backmeupplz/project-horae/media/2026-10-05/cad-charger.png

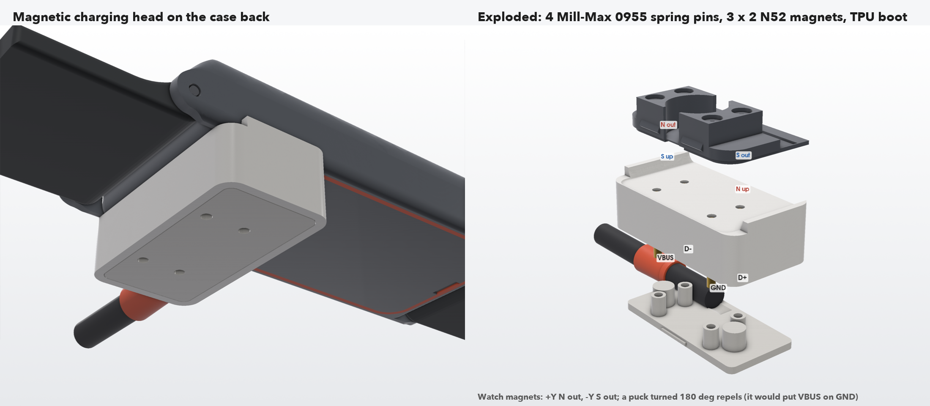
media/2026-10-05/cad-charger.png
