backmeupplz/project-horae/explorer/face.png

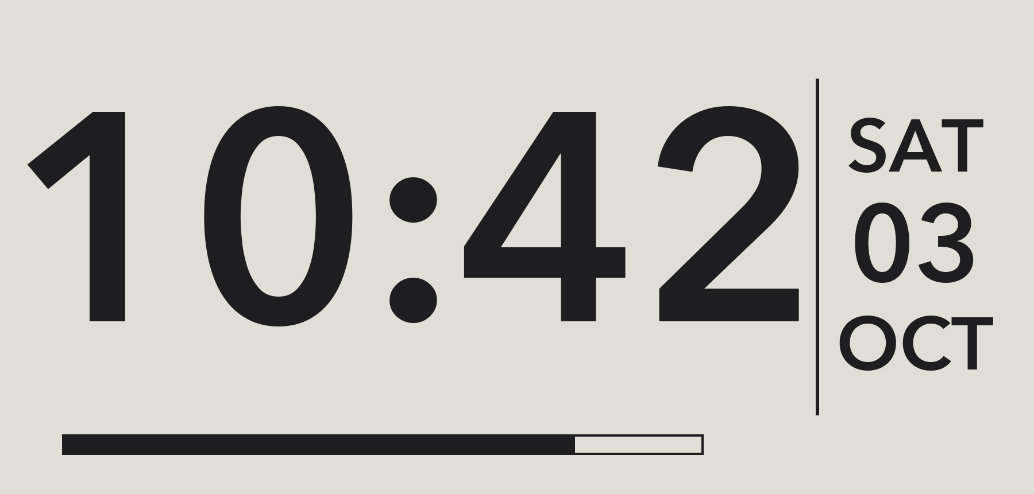
explorer/face.png
