backmeupplz/project-horae/hardware/out/panel-top.png

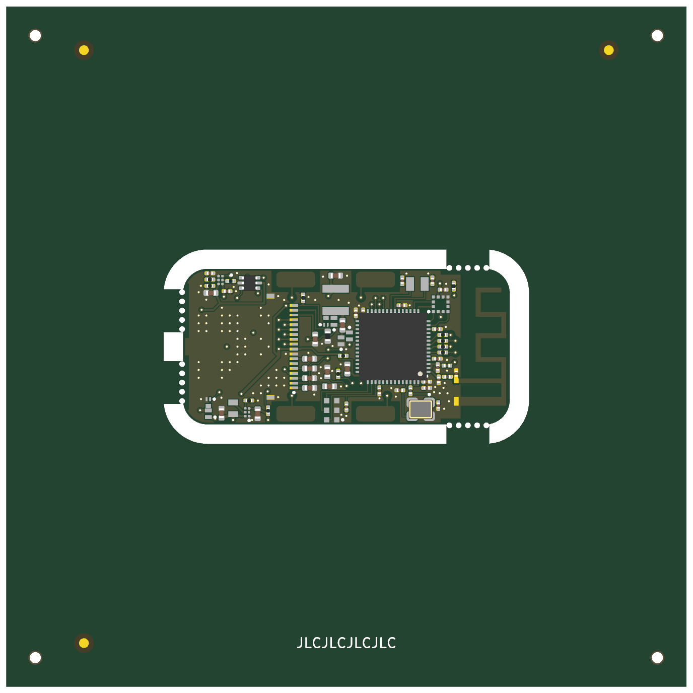
hardware/out/panel-top.png
