backmeupplz/project-horae/hardware/out/pcb-top.png

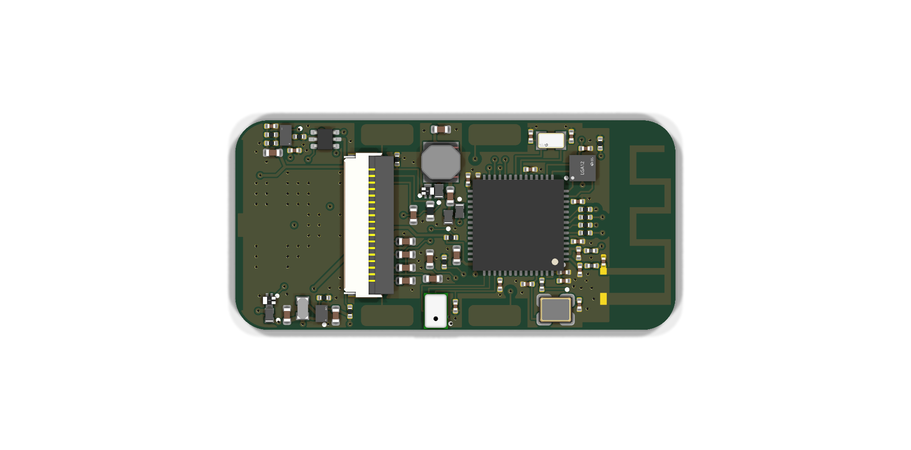
hardware/out/pcb-top.png
