backmeupplz/project-horae/hardware/rf/geom.png

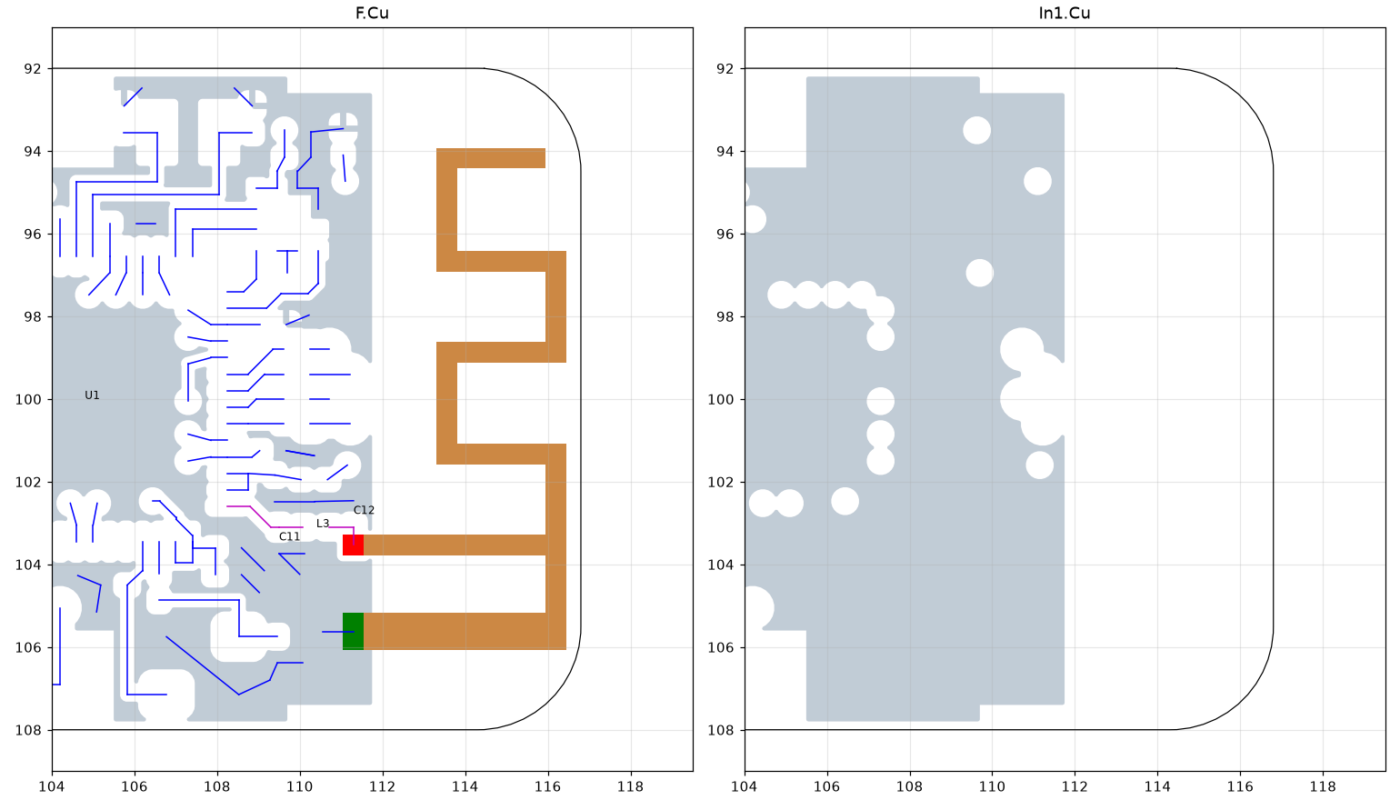
hardware/rf/geom.png
