backmeupplz/project-horae/hardware/rf/rf-s11.png

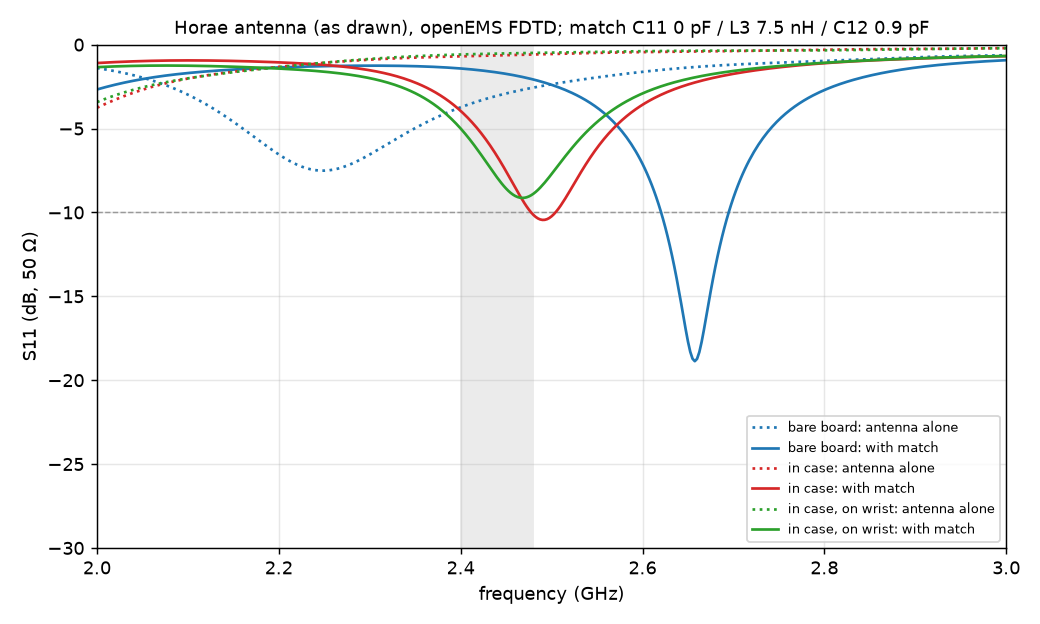
hardware/rf/rf-s11.png
