backmeupplz/project-horae/hardware/rf/rf-s11_v4_trim6.64.png

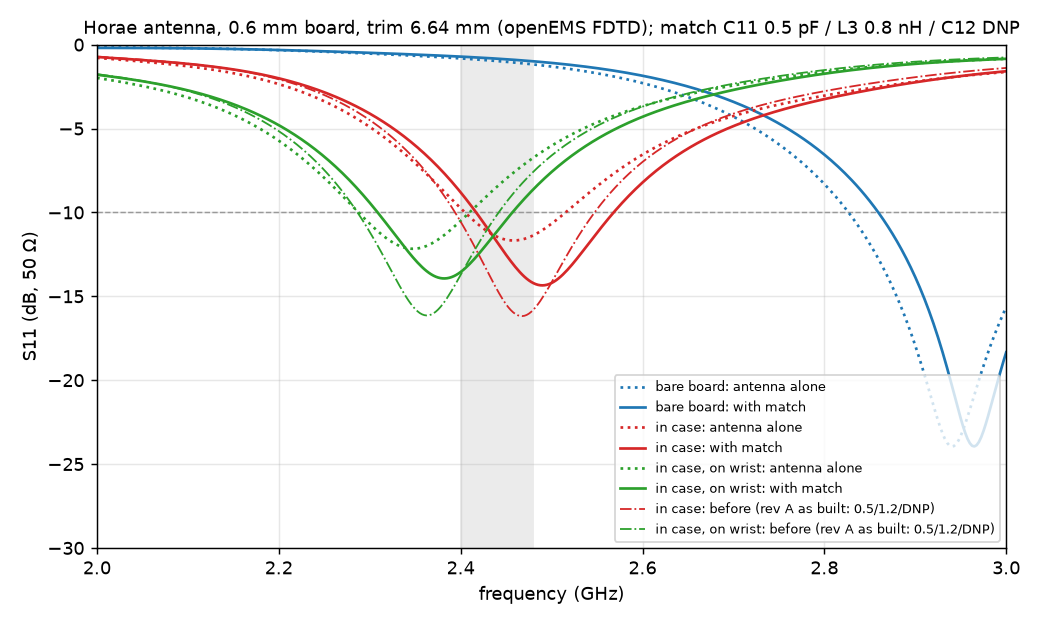
hardware/rf/rf-s11_v4_trim6.64.png
