backmeupplz/project-horae/hardware/rf/rf-smith_trim6.64.png

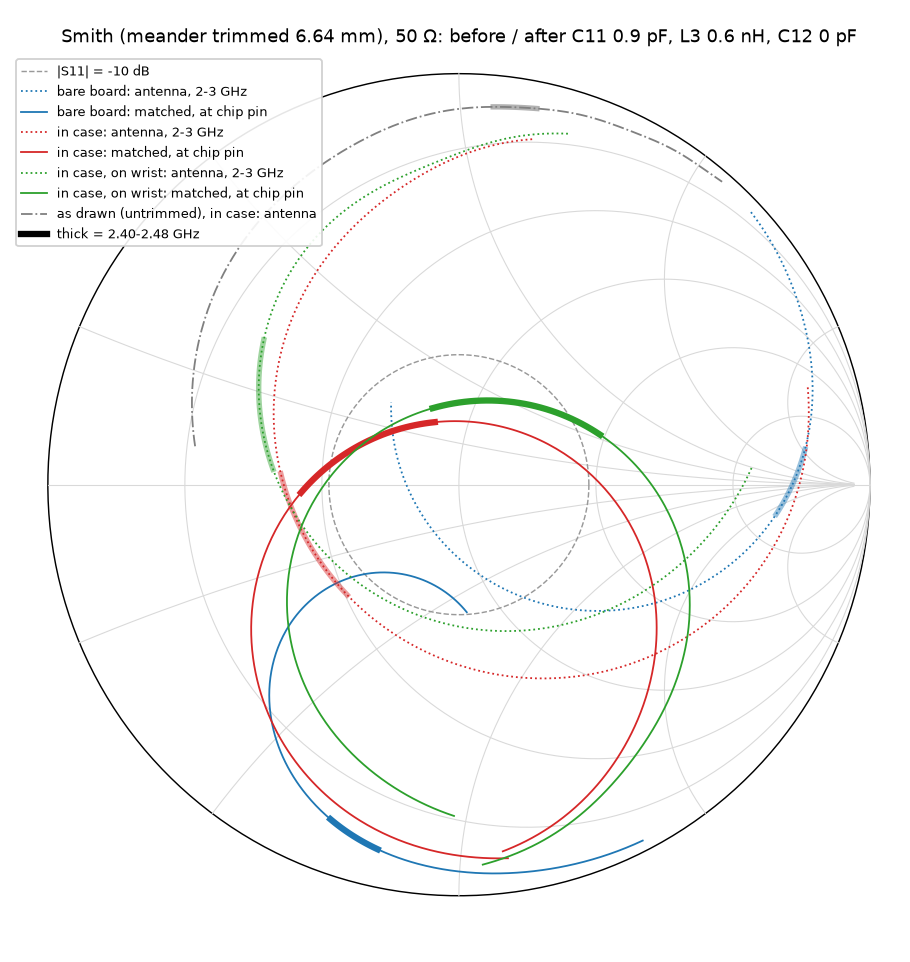
hardware/rf/rf-smith_trim6.64.png
