backmeupplz/project-horae/media/2026-10-03/box.jpg

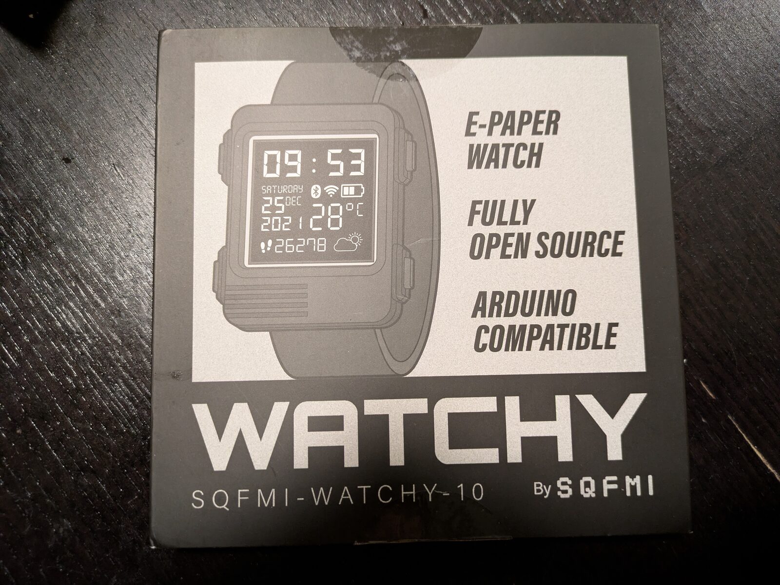
media/2026-10-03/box.jpg
