backmeupplz/project-horae/media/2026-10-03/inner-box.jpg

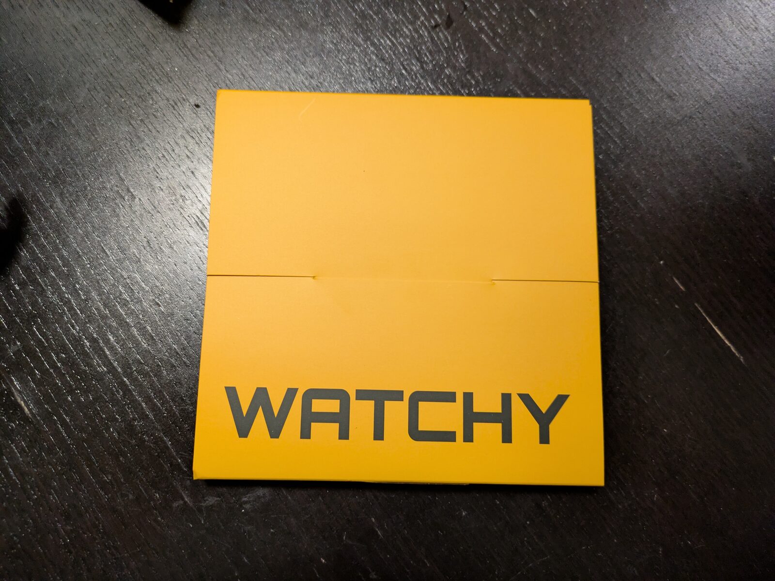
media/2026-10-03/inner-box.jpg
