backmeupplz/project-horae/media/2026-10-03/open.jpg

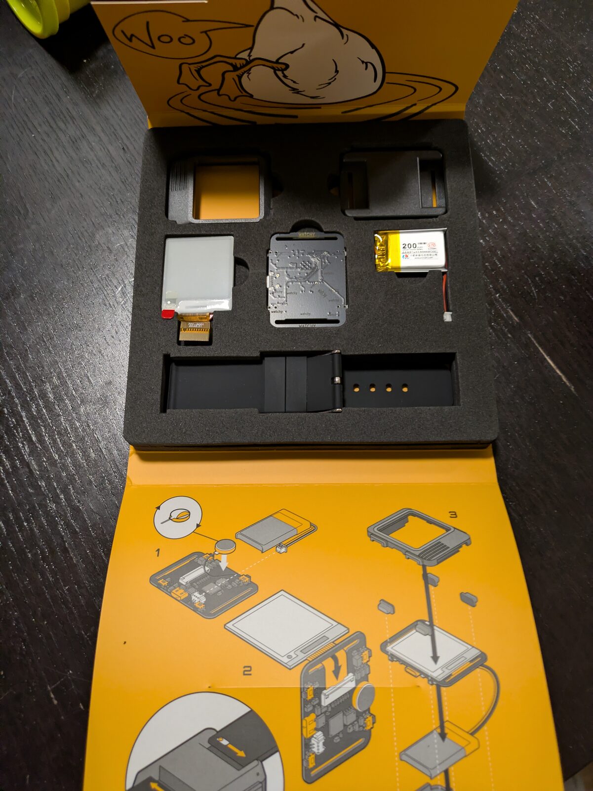
media/2026-10-03/open.jpg
