backmeupplz/project-horae/media/2026-10-04/cad-dock.png

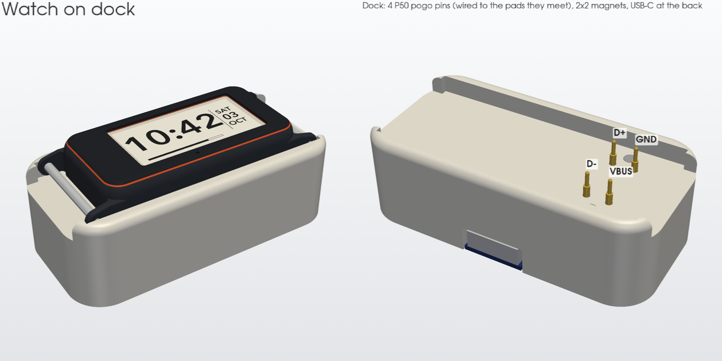
media/2026-10-04/cad-dock.png
