backmeupplz/project-horae/media/2026-10-04/cad-exploded.png

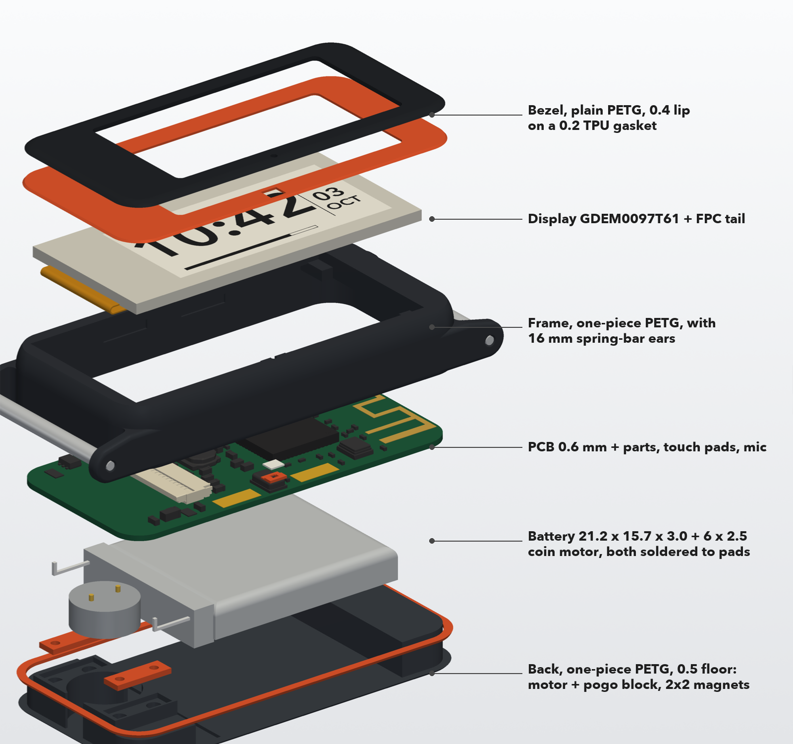
media/2026-10-04/cad-exploded.png
