backmeupplz/project-horae/media/2026-10-04/cad-mic.png

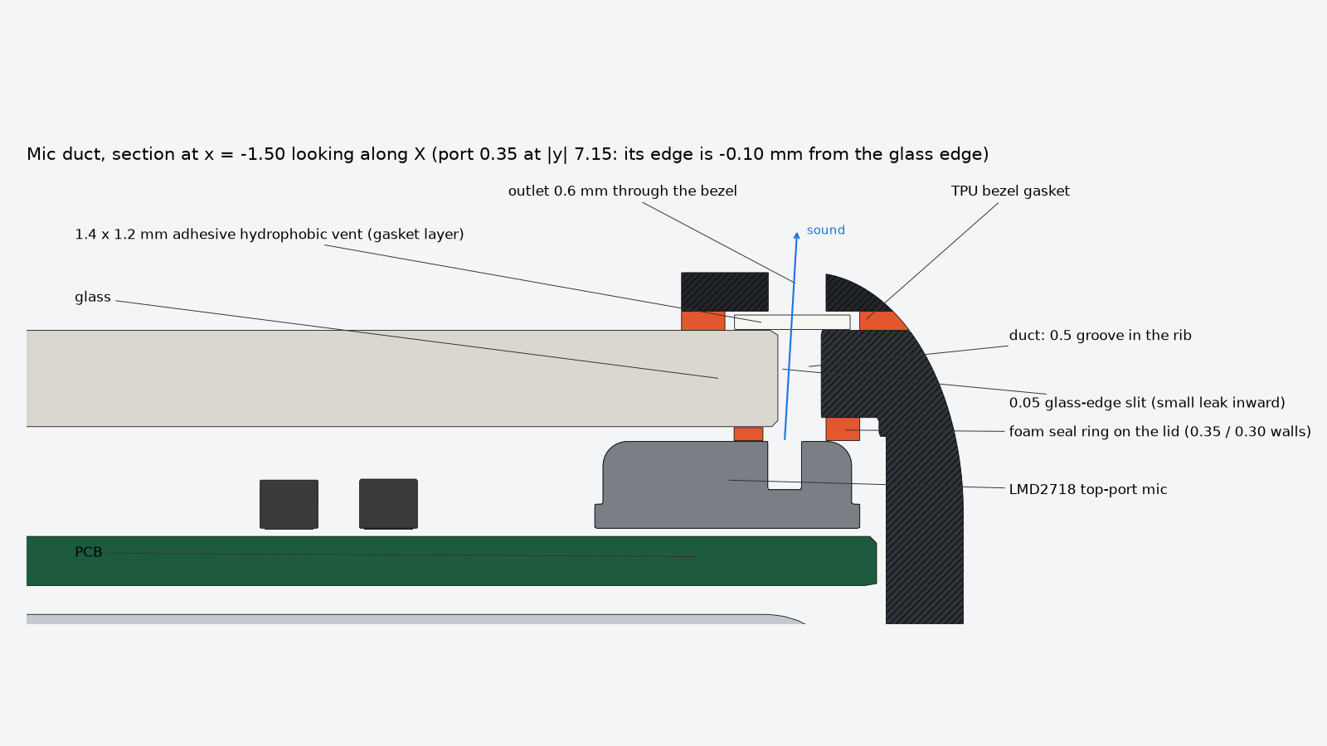
media/2026-10-04/cad-mic.png
