backmeupplz/project-horae/media/2026-10-04/cad-scale.png

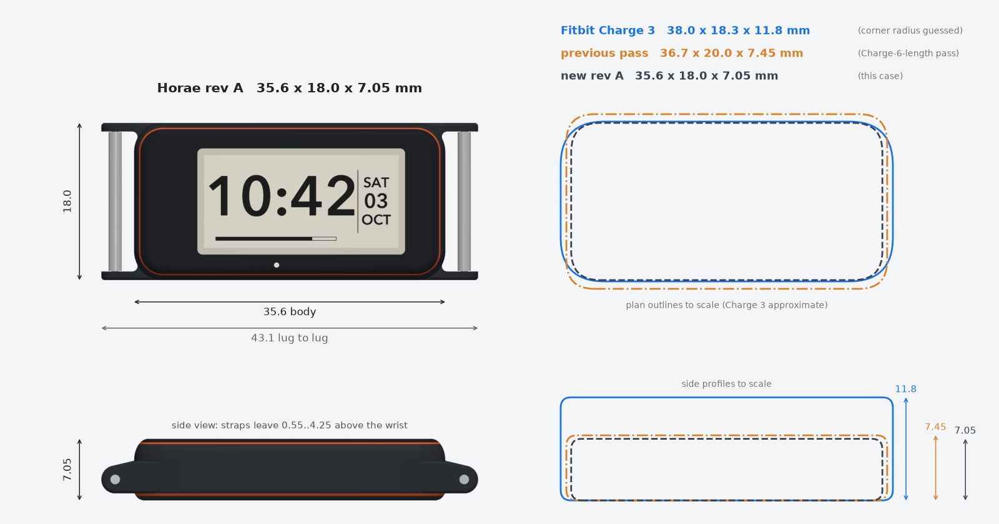
media/2026-10-04/cad-scale.png
