backmeupplz/project-horae/media/2026-10-04/cad-sealing.png

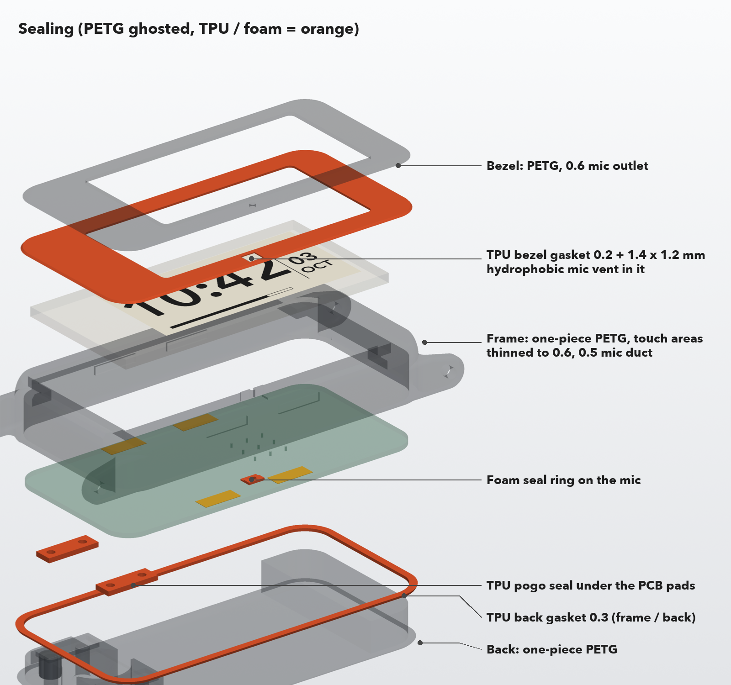
media/2026-10-04/cad-sealing.png
