backmeupplz/project-horae/media/2026-10-04/cad-section.png

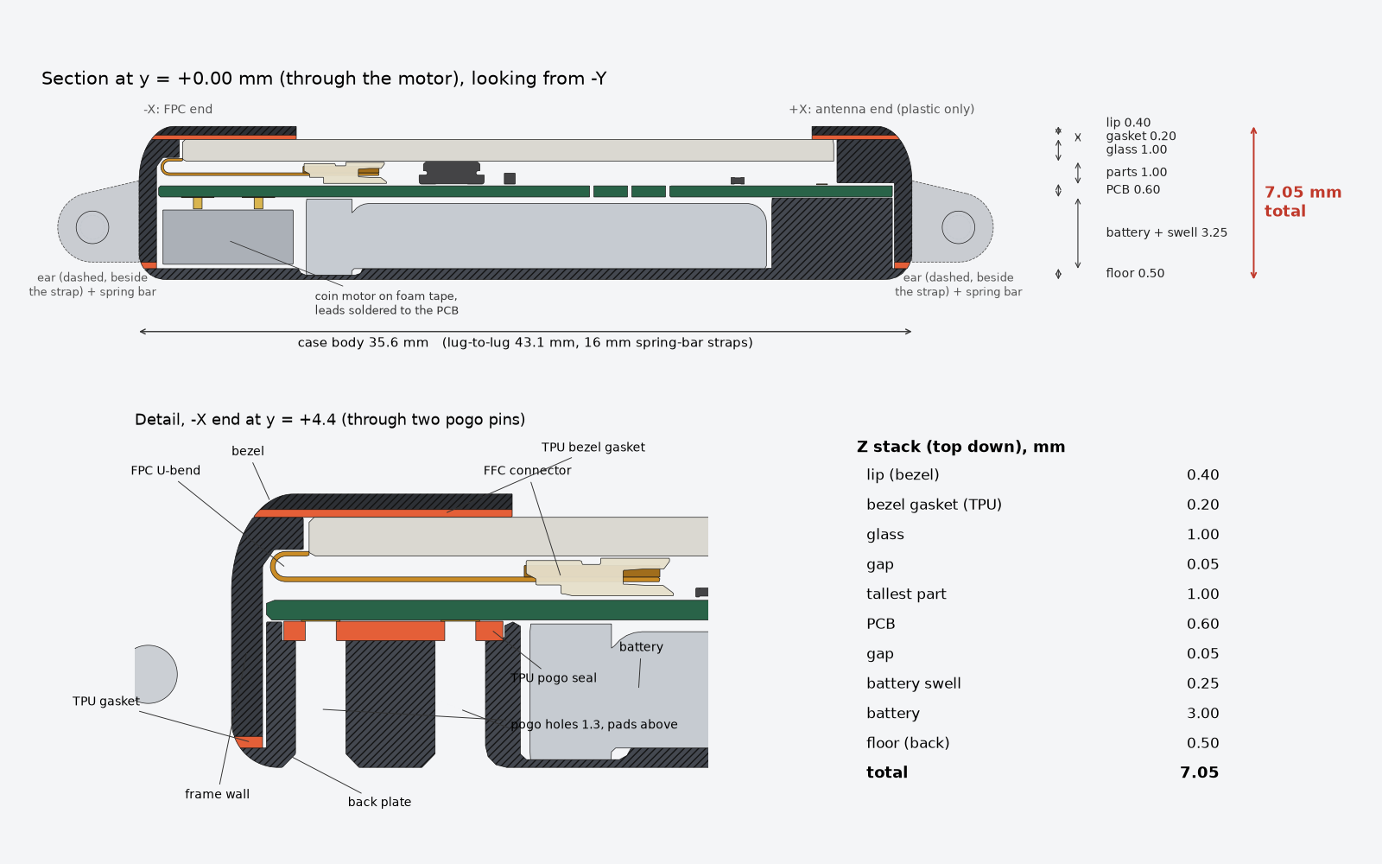
media/2026-10-04/cad-section.png
