backmeupplz/project-horae/media/2026-10-04/cad-shape-options.png

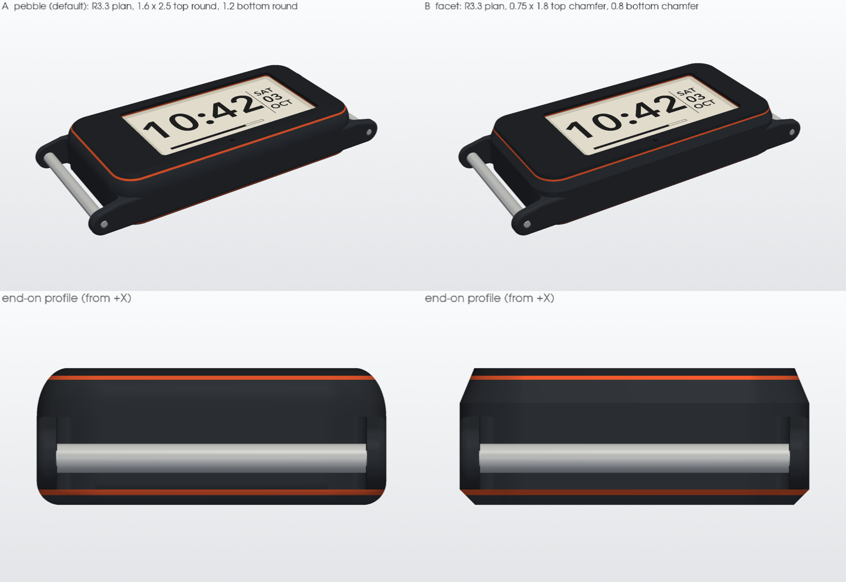
media/2026-10-04/cad-shape-options.png
