backmeupplz/project-horae/media/2026-10-04/pcb-3d.png

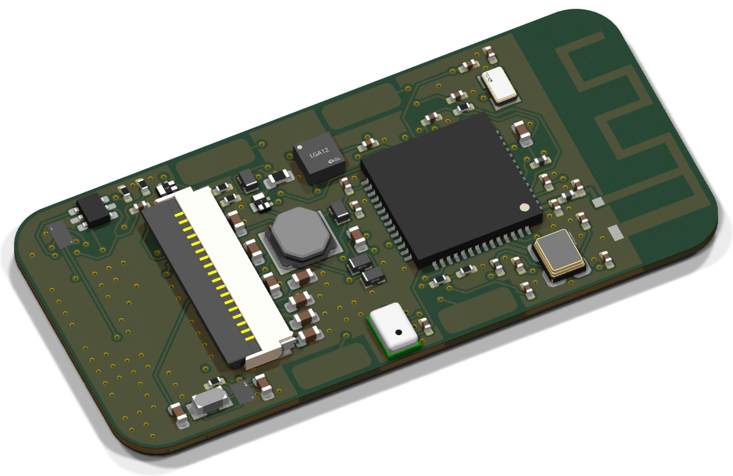
media/2026-10-04/pcb-3d.png
