backmeupplz/project-horae/media/2026-10-04/pcb-bottom.png

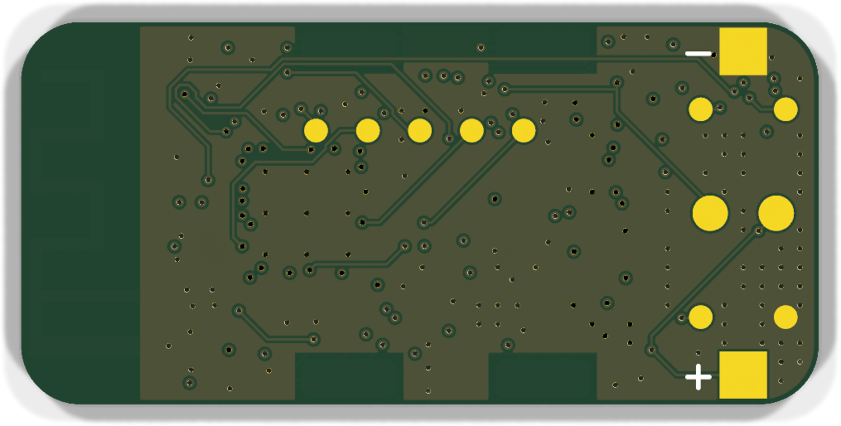
media/2026-10-04/pcb-bottom.png
