backmeupplz/project-horae/media/2026-10-04/pcb-copper.png

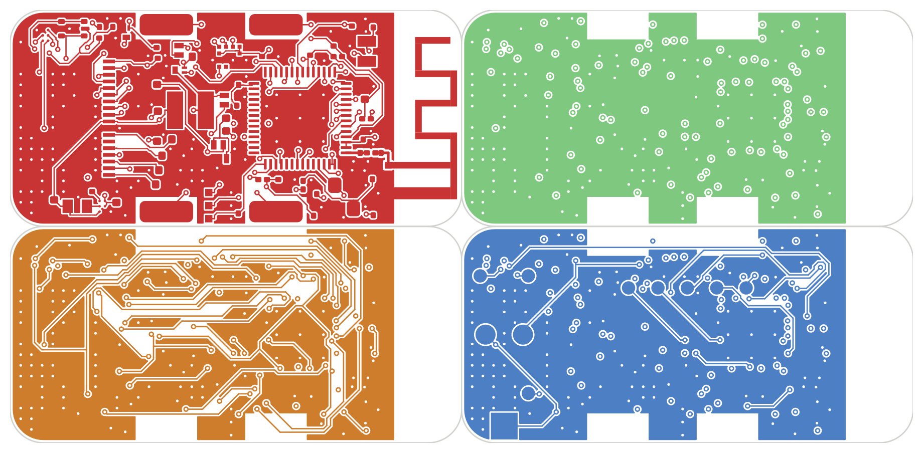
media/2026-10-04/pcb-copper.png
