backmeupplz/project-horae/media/2026-10-04/pcb-rf.png

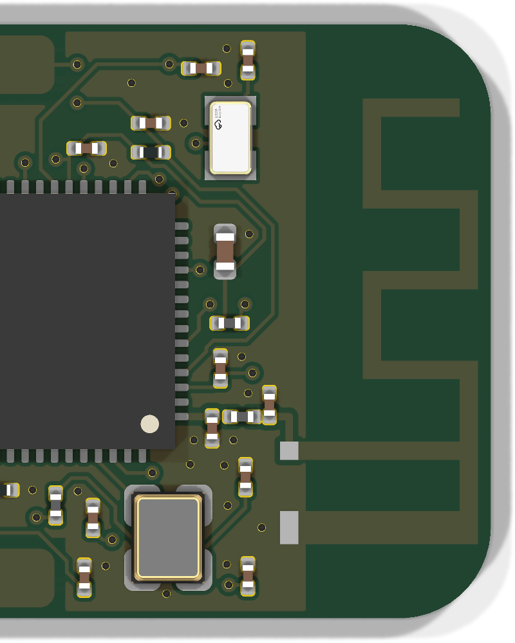
media/2026-10-04/pcb-rf.png
