backmeupplz/project-horae/media/2026-10-04/pcb-top.png

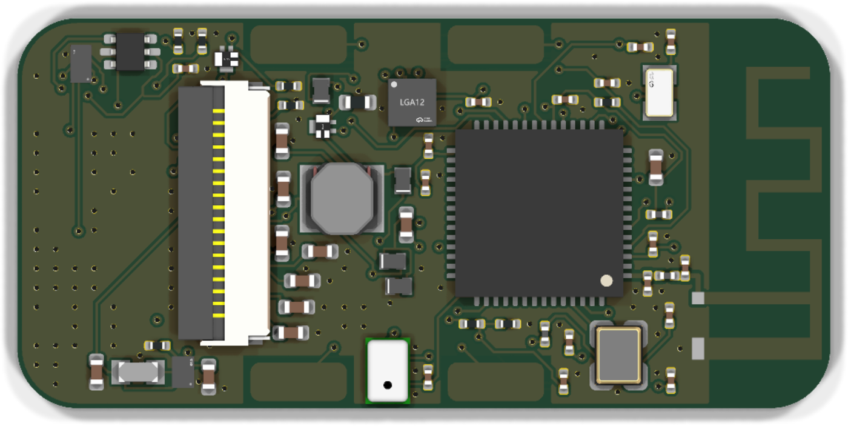
media/2026-10-04/pcb-top.png
