backmeupplz/project-horae/media/2026-10-04/rf-s11.png

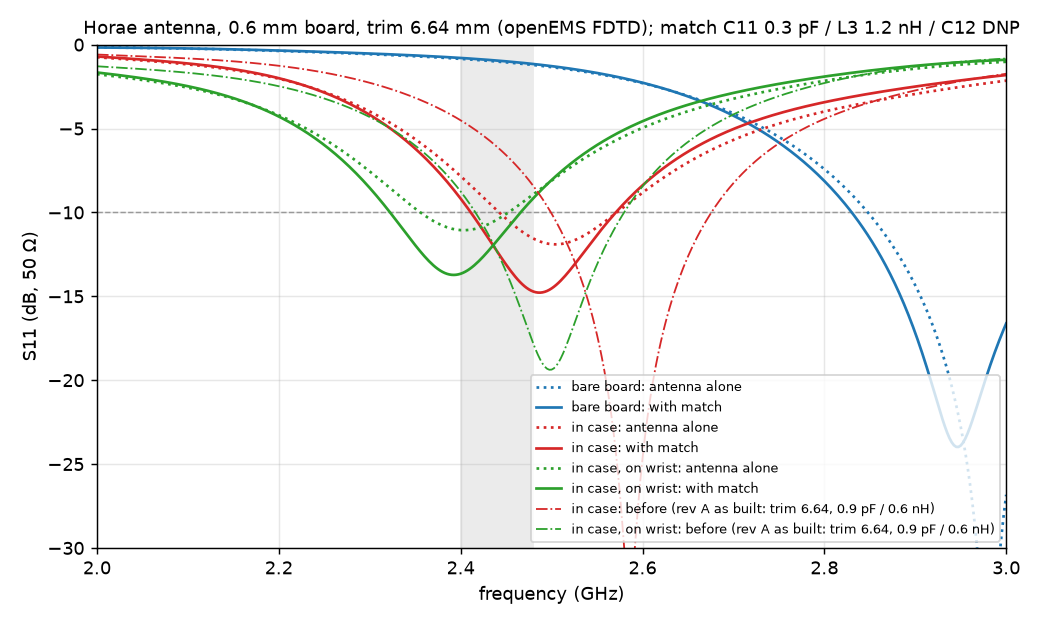
media/2026-10-04/rf-s11.png
