backmeupplz/project-horae/media/2026-10-04/rf-smith.png

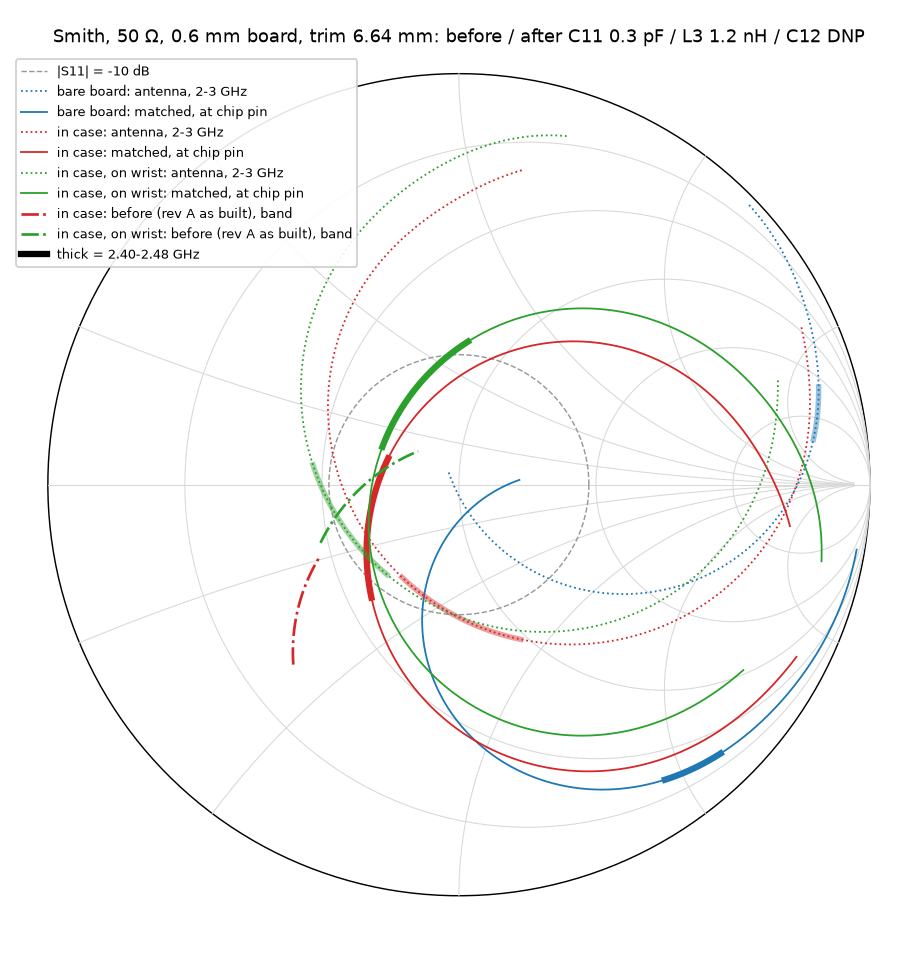
media/2026-10-04/rf-smith.png
