backmeupplz/project-horae/media/2026-10-05/cad-colors.png

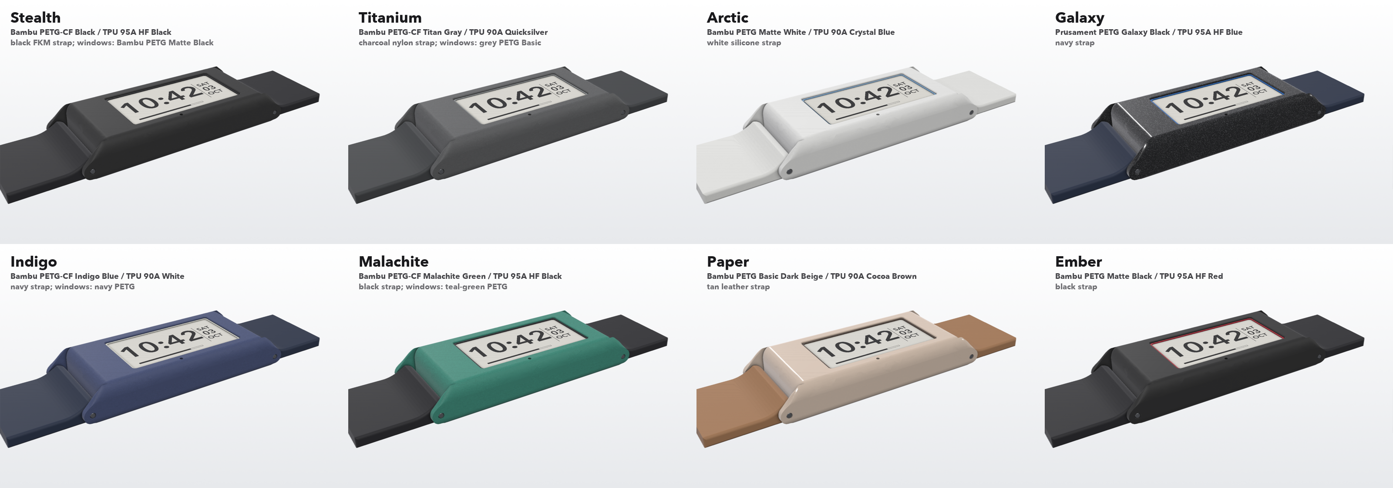
media/2026-10-05/cad-colors.png
