backmeupplz/project-horae/media/2026-10-05/cad-exploded.png

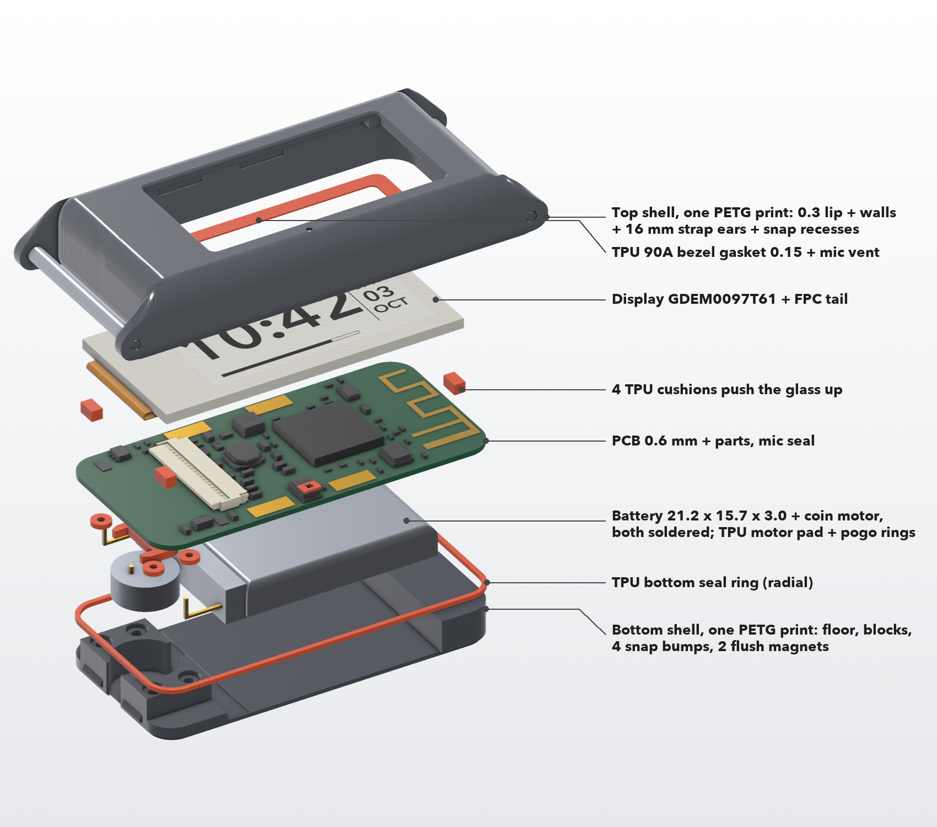
media/2026-10-05/cad-exploded.png
