backmeupplz/project-horae/media/2026-10-05/cad-lug.png

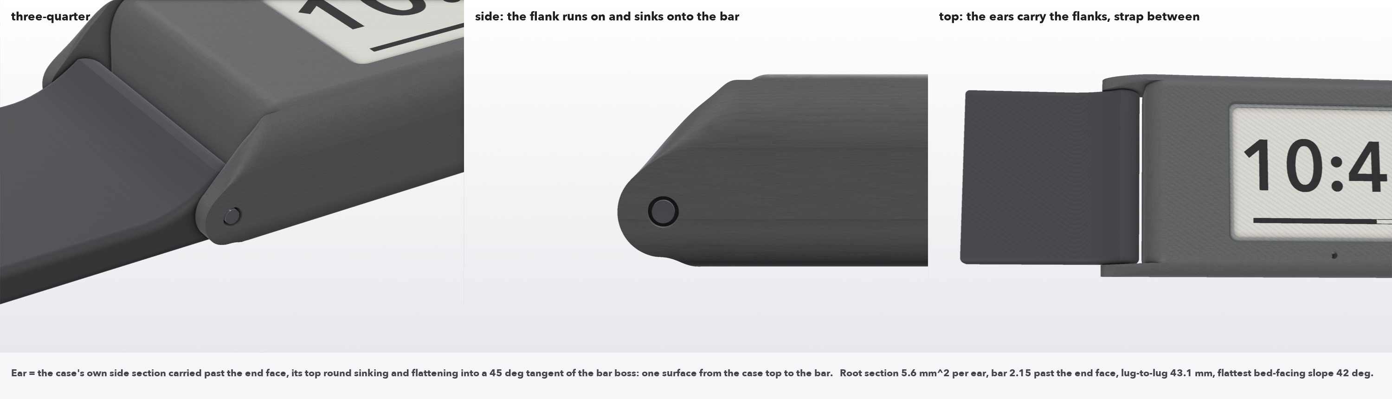
media/2026-10-05/cad-lug.png
