backmeupplz/project-horae/media/2026-10-05/cad-mic.png

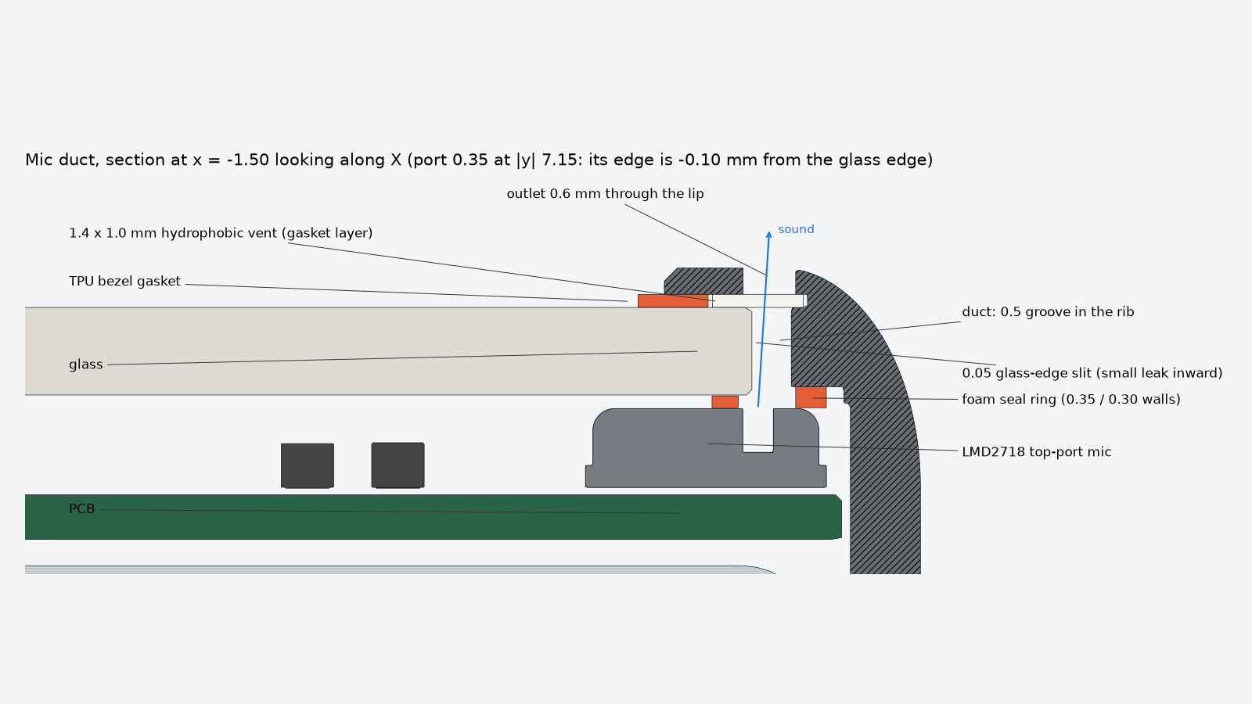
media/2026-10-05/cad-mic.png
