backmeupplz/project-horae/media/2026-10-05/cad-scale.png

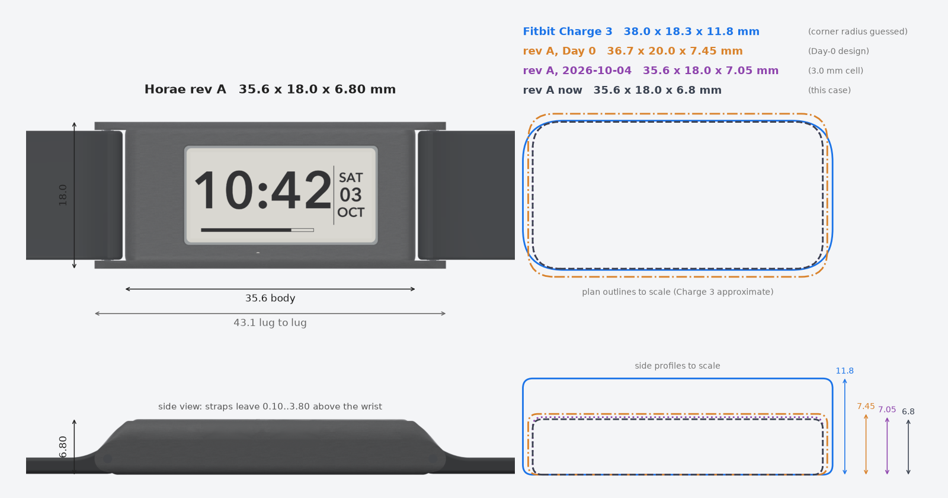
media/2026-10-05/cad-scale.png
