backmeupplz/project-horae/media/2026-10-05/cad-sealing.png

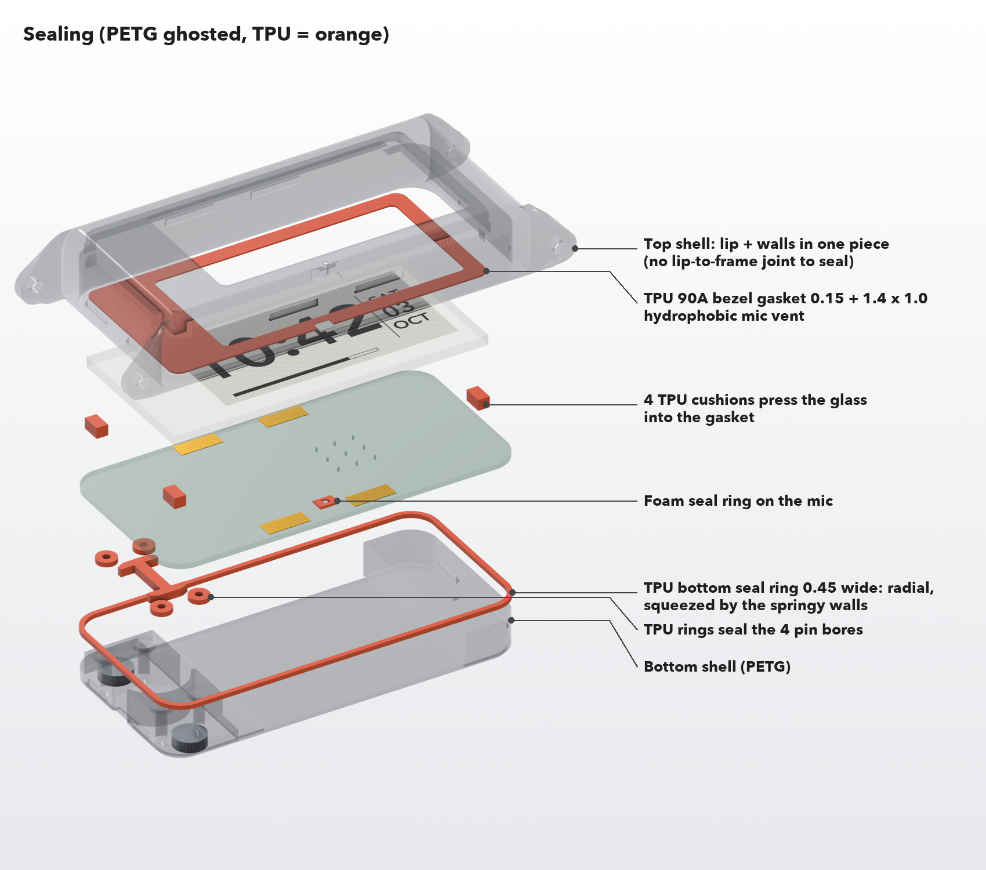
media/2026-10-05/cad-sealing.png
