backmeupplz/project-horae/media/2026-10-05/cad-section.png

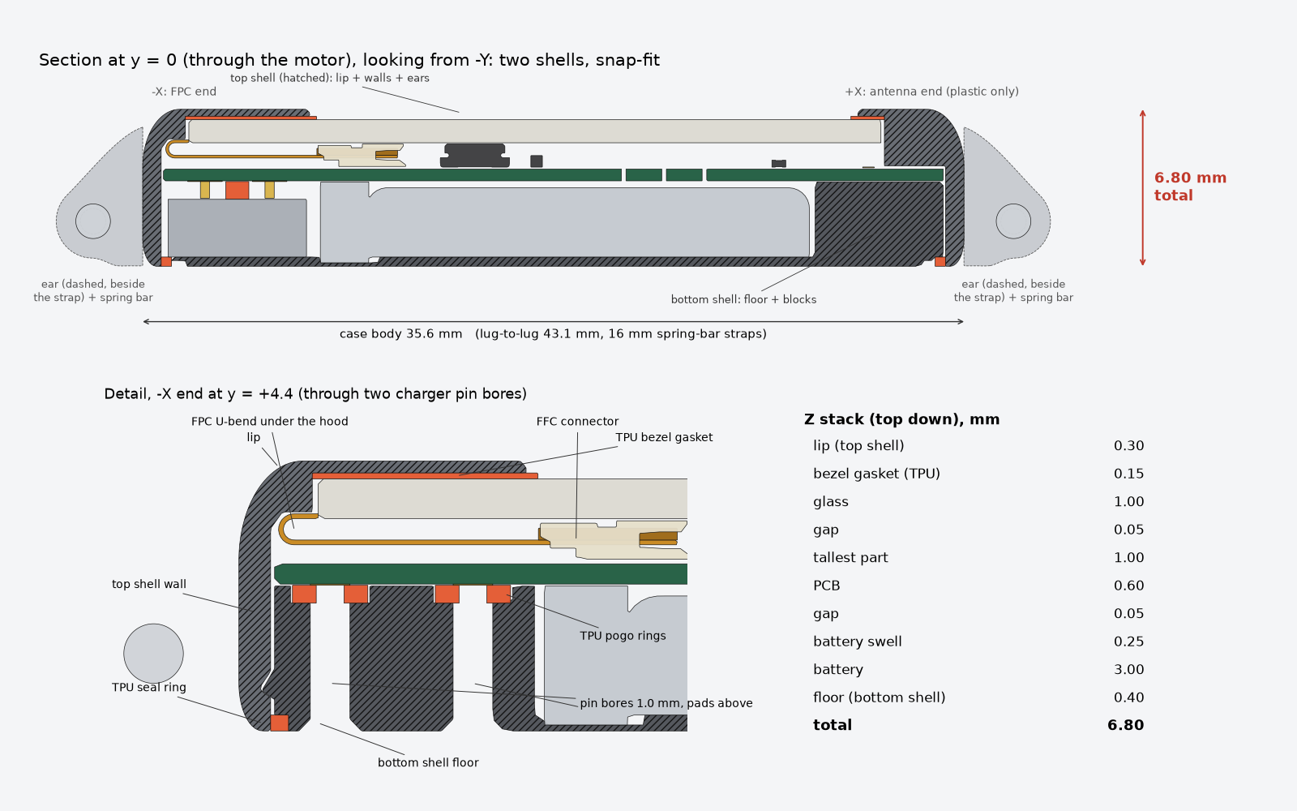
media/2026-10-05/cad-section.png
