backmeupplz/project-horae/media/2026-10-05/cad-shape-options.png

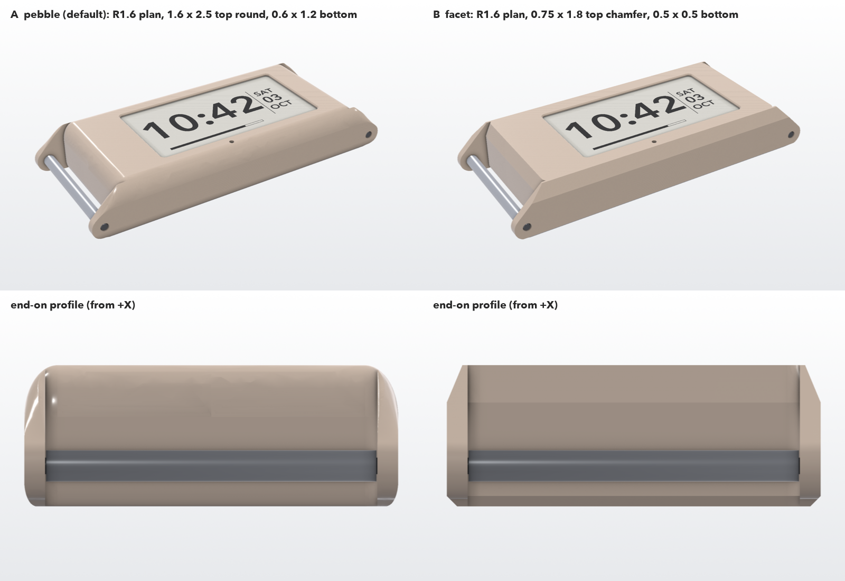
media/2026-10-05/cad-shape-options.png
