backmeupplz/project-horae/media/2026-10-05/cad-snap.png

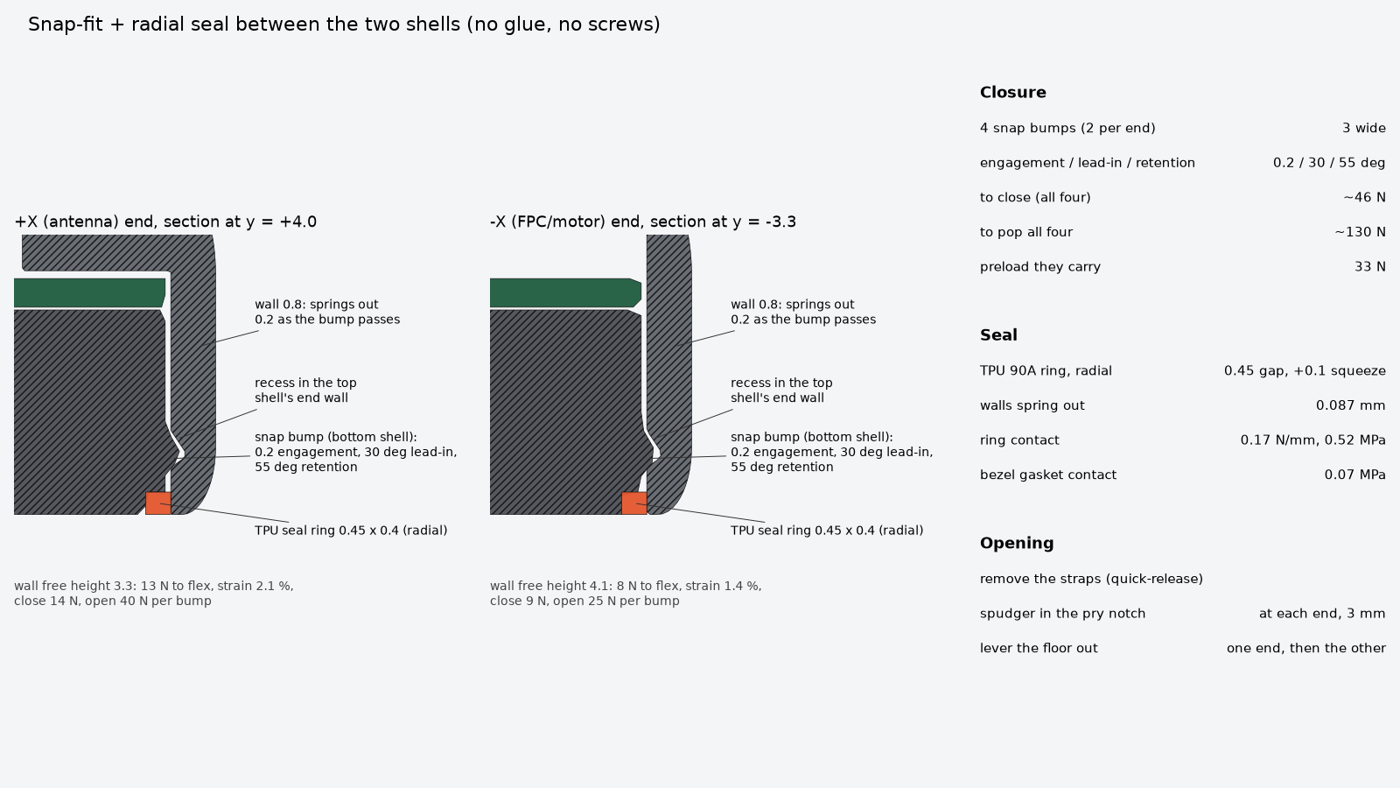
media/2026-10-05/cad-snap.png
