backmeupplz/project-horae/media/2026-10-05/rf-smith.png

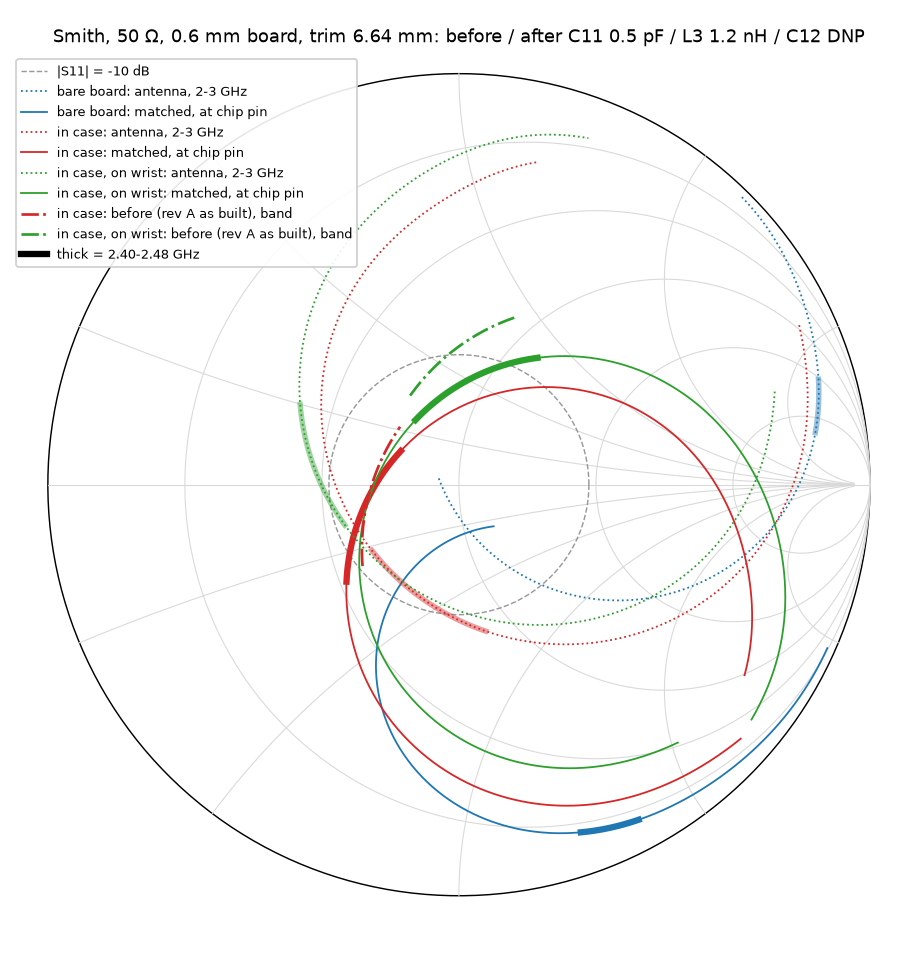
media/2026-10-05/rf-smith.png
