backmeupplz/project-horae/media/2026-10-06/board-bottom.png

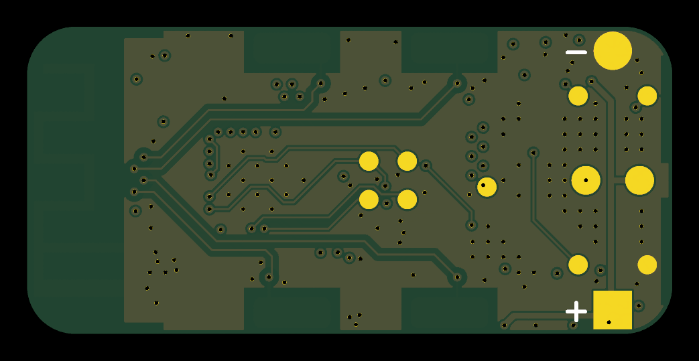
media/2026-10-06/board-bottom.png
