backmeupplz/project-horae/media/2026-10-06/board-top.png

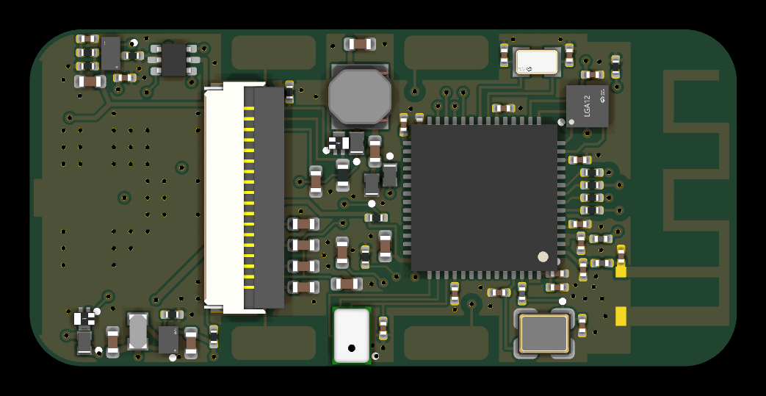
media/2026-10-06/board-top.png
