backmeupplz/project-horae/media/2026-10-06/cad-board-in-case.png

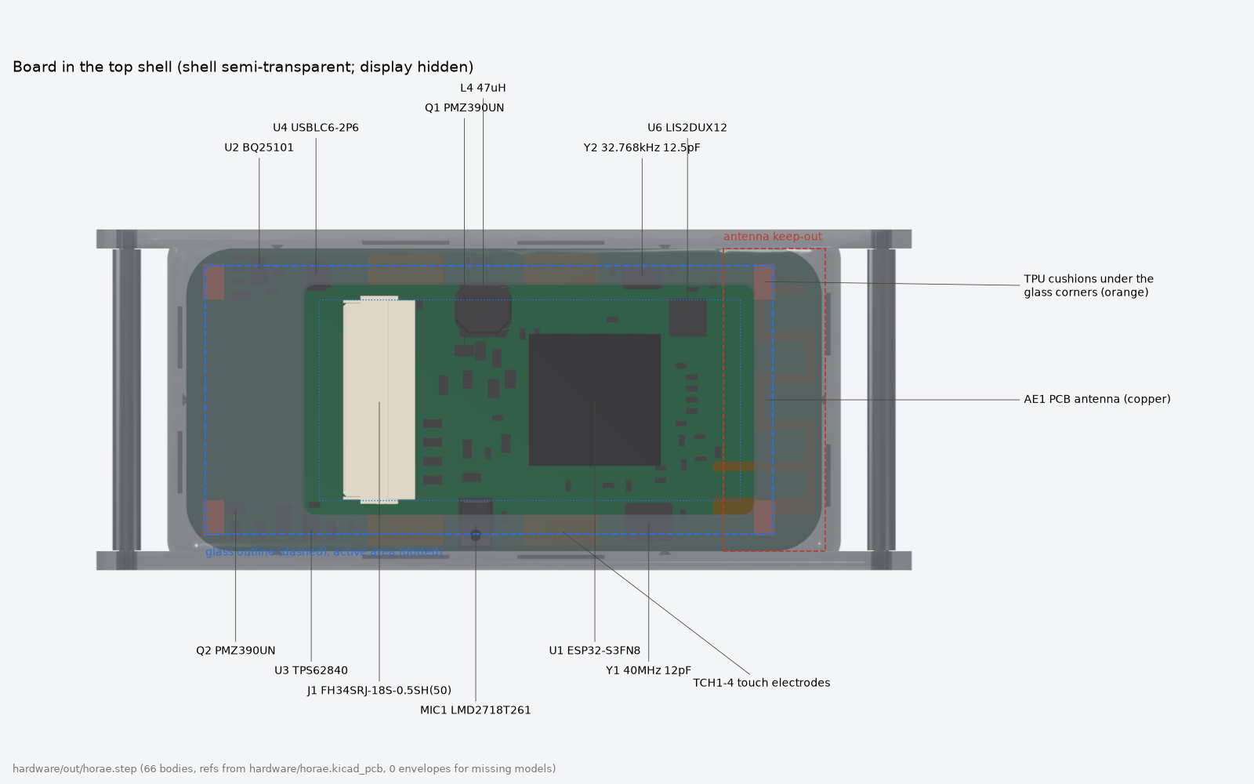
media/2026-10-06/cad-board-in-case.png
