backmeupplz/project-horae/media/2026-10-06/cad-dock.png

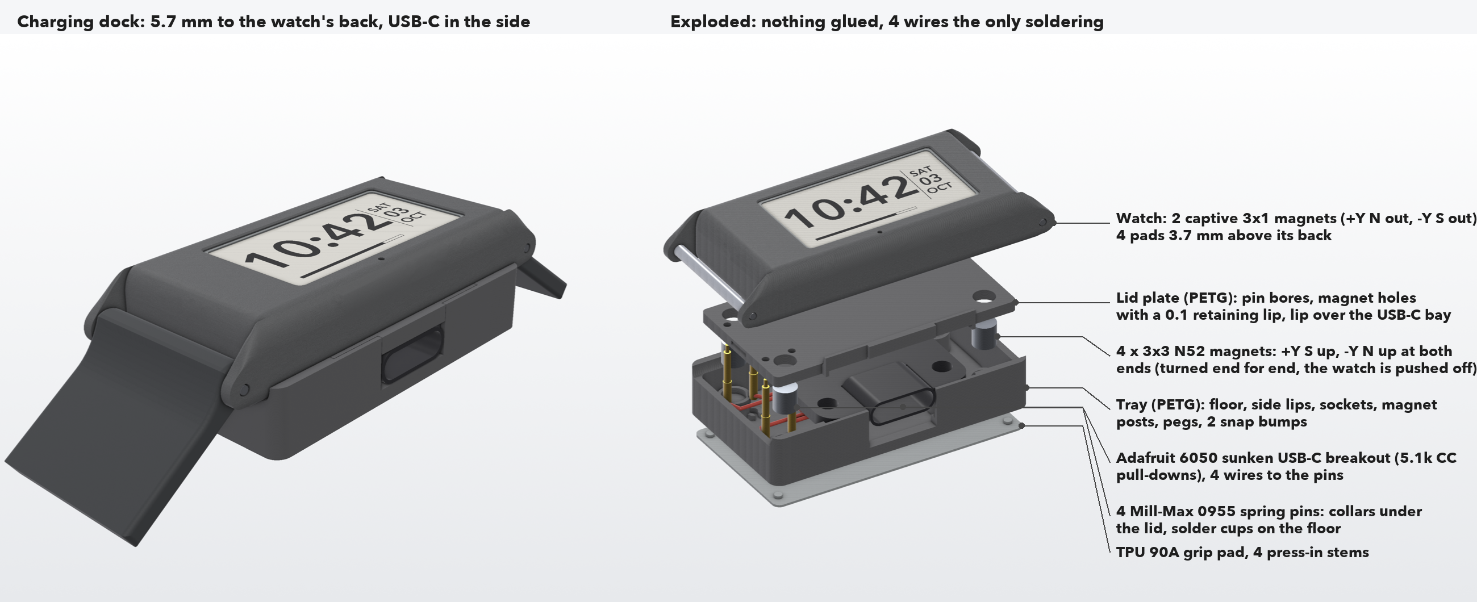
media/2026-10-06/cad-dock.png
