backmeupplz/project-horae/media/2026-10-06/explorer-dock-exploded.png

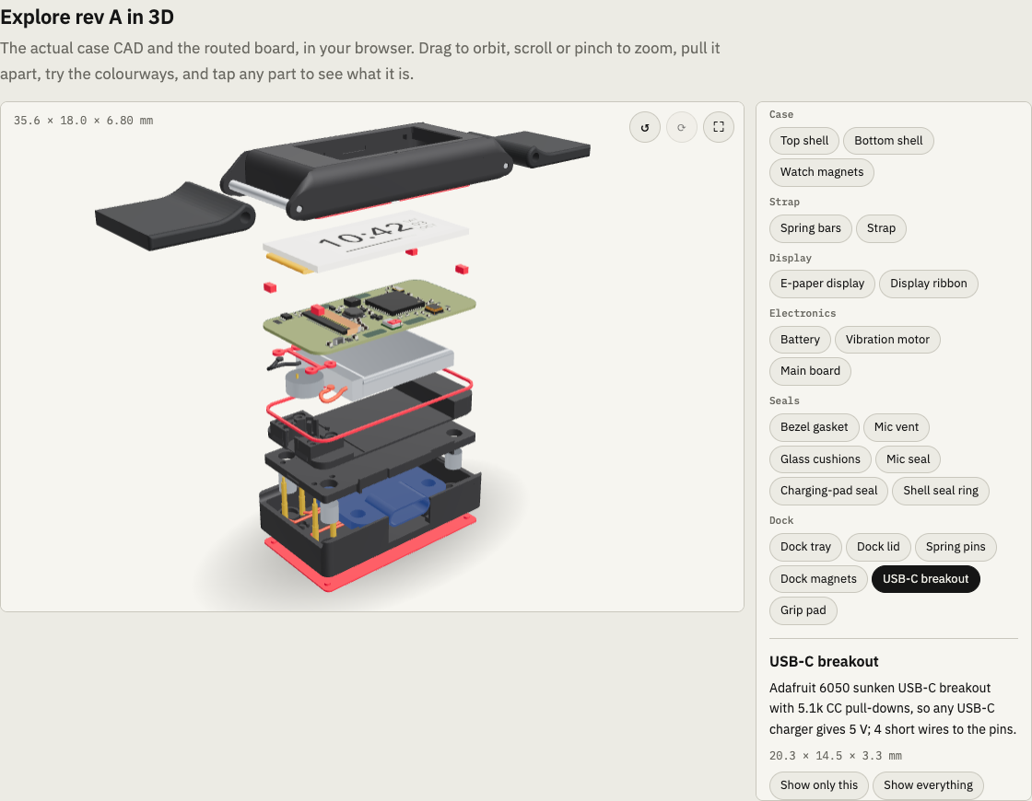
media/2026-10-06/explorer-dock-exploded.png
