backmeupplz/project-horae/media/2026-10-06/explorer-dock.png

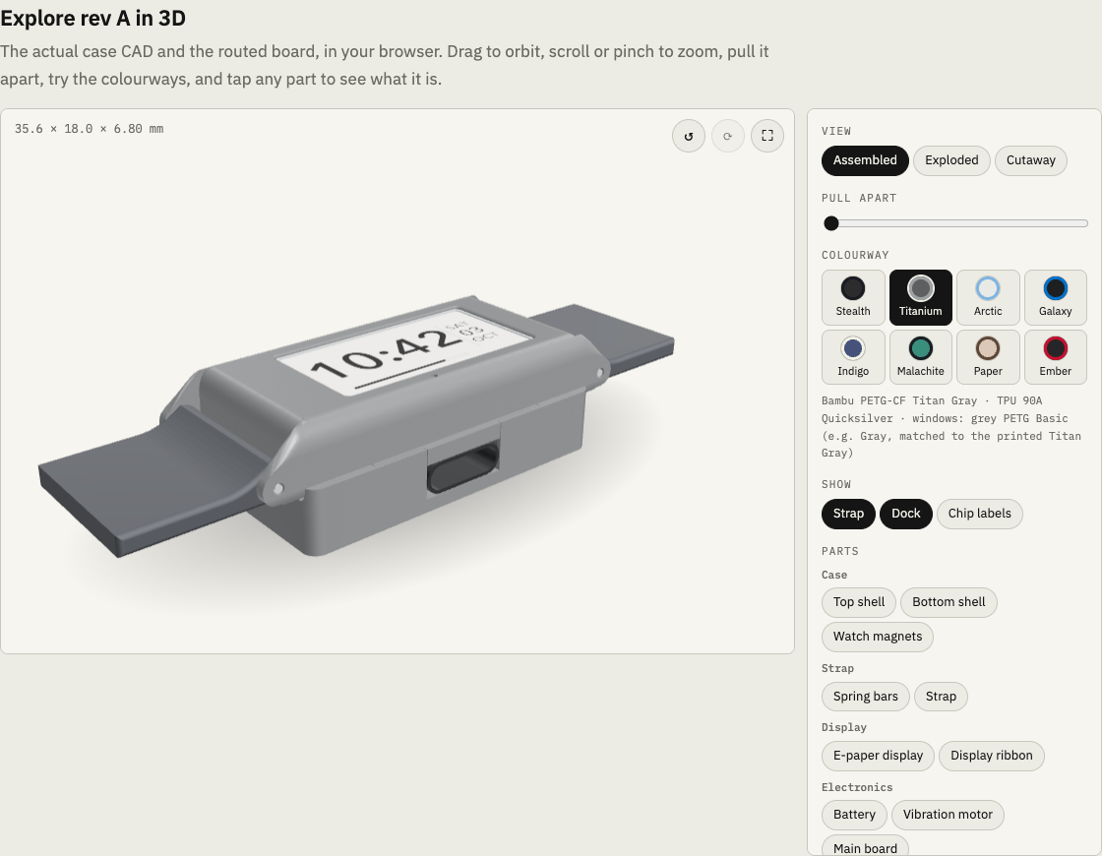
media/2026-10-06/explorer-dock.png
