backmeupplz/project-horae/og.png

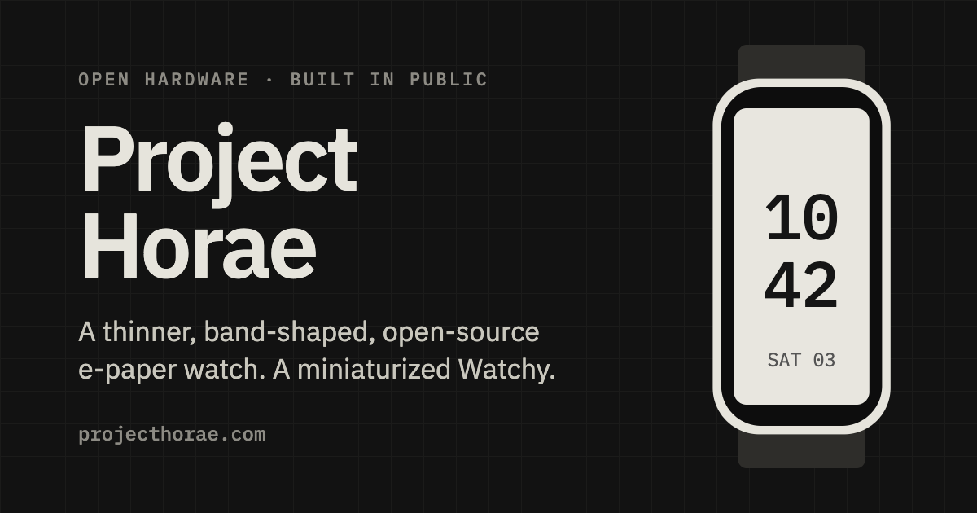
og.png
