backmeupplz/project-horae/cad/out/variant-thin/dock/dock_lid.3mf

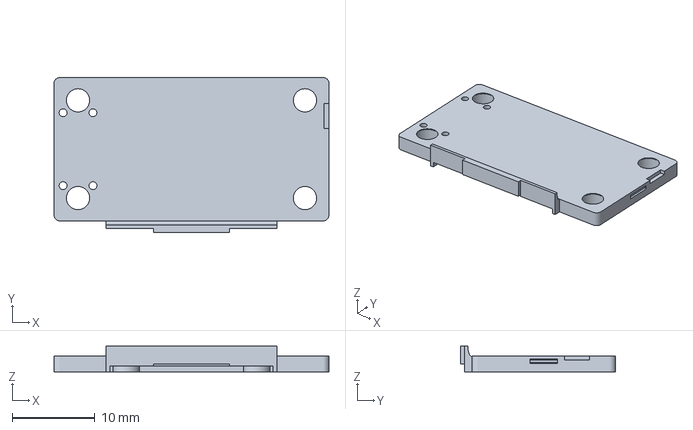
[picture p65: CAD file, 2026-10-07]
cad/out/variant-thin/dock/dock_lid.3mf
33.2 x 18.7 x 3.12 mm
