backmeupplz/project-horae/cad/out/variant-thin/petg/bottom_shell.3mf

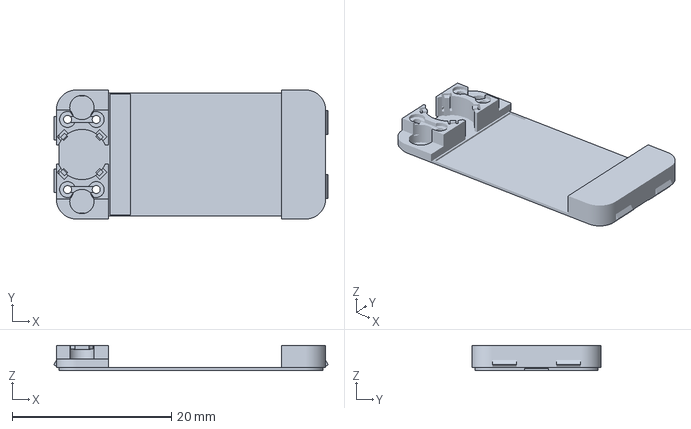
[picture p66: CAD file, 2026-10-07]
cad/out/variant-thin/petg/bottom_shell.3mf
34.4 x 16.2 x 3.15 mm
