backmeupplz/project-horae/cad/out/variant-thin/plates/petg-cf-set.3mf

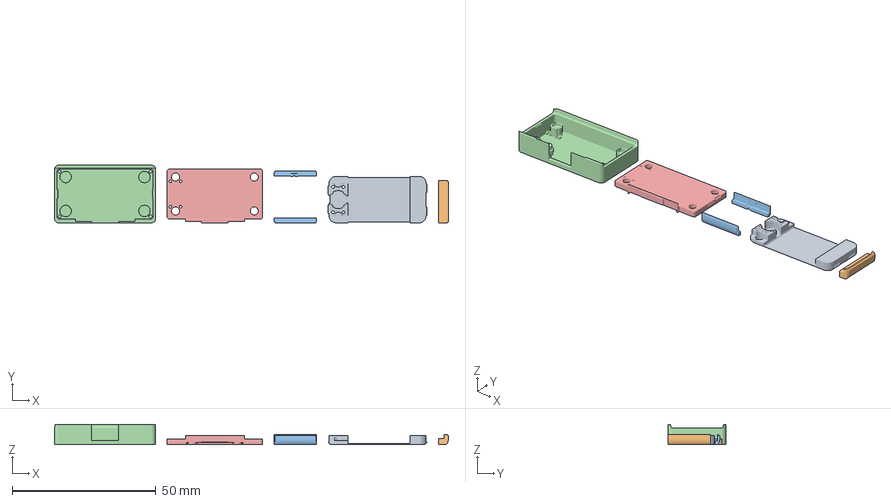
[picture p67: CAD file, 2026-10-07]
cad/out/variant-thin/plates/petg-cf-set.3mf
137.1 x 20.1 x 7.08 mm
bottom_shell
antenna_window
touch_windows
dock_base
dock_lid
