backmeupplz/project-horae/cad/out/variant-thin/tpu/cushions.3mf

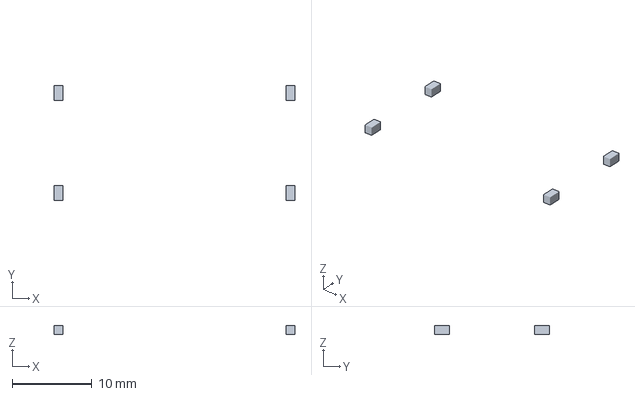
[picture p68: CAD file, 2026-10-07]
cad/out/variant-thin/tpu/cushions.3mf
30.2 x 14.4 x 1.15 mm
