backmeupplz/project-horae/cad/out/plates/petg-cf-set.3mf

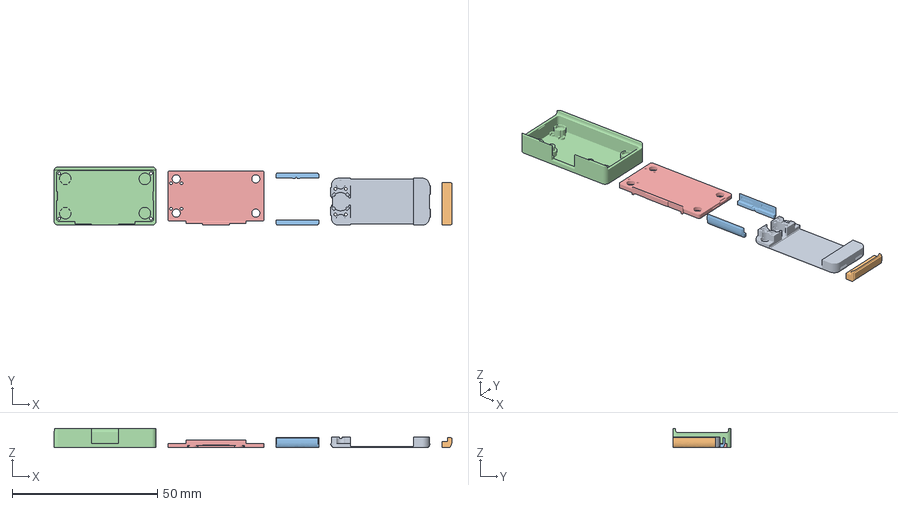
[picture p69: CAD file, 2026-10-07]
cad/out/plates/petg-cf-set.3mf
137.1 x 20.1 x 6.58 mm
bottom_shell
antenna_window
touch_windows
dock_base
dock_lid
