backmeupplz/project-horae/cad/out/tpu/pogo_seals.3mf

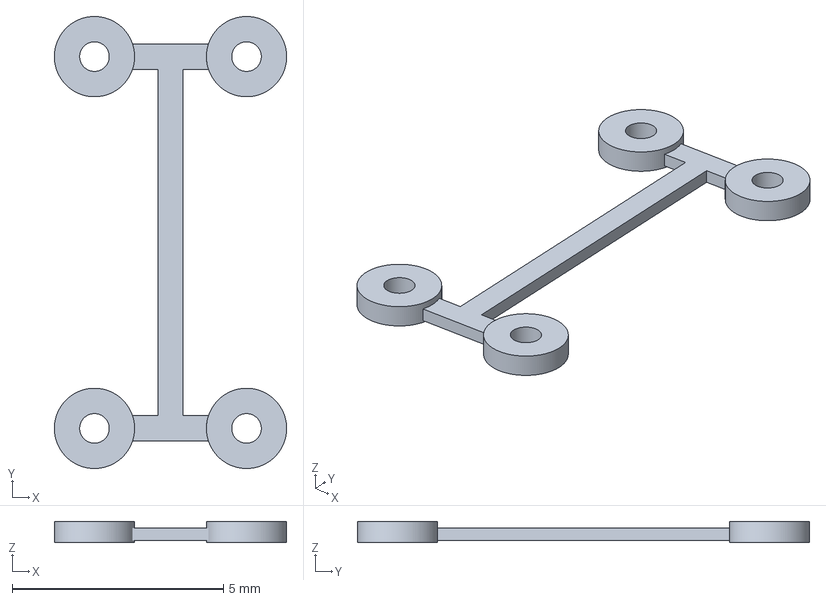
[picture p70: CAD file, 2026-10-07]
cad/out/tpu/pogo_seals.3mf
5.50 x 10.7 x 0.5 mm
