backmeupplz/project-horae/cad/out/variant-thin/dock/dock_base.3mf

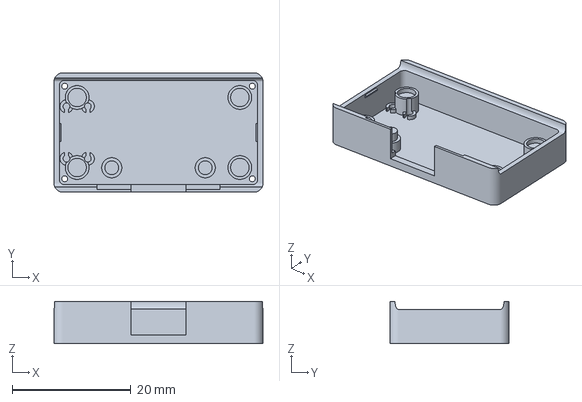
[picture p71: CAD file, 2026-10-07]
cad/out/variant-thin/dock/dock_base.3mf
35.2 x 20.1 x 7.08 mm
