backmeupplz/project-horae/cad/out/variant-thin/plates/petg-cf.3mf

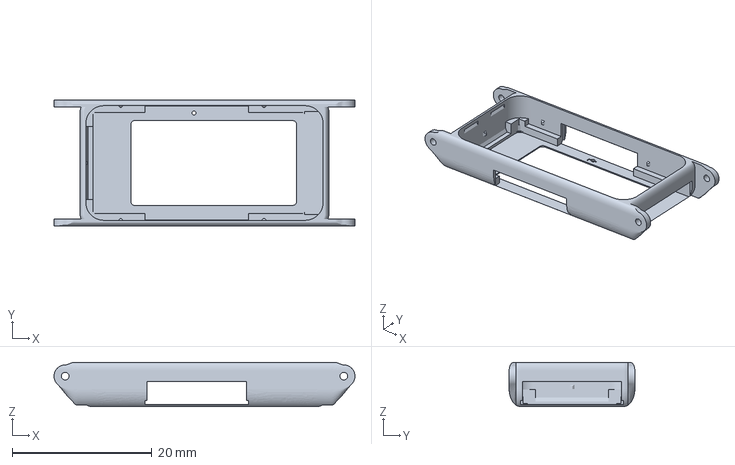
[picture p72: CAD file, 2026-10-07]
cad/out/variant-thin/plates/petg-cf.3mf
43.1 x 18.0 x 6.30 mm
