backmeupplz/project-horae/cad/out/variant-thin/tpu/bezel_gasket.3mf

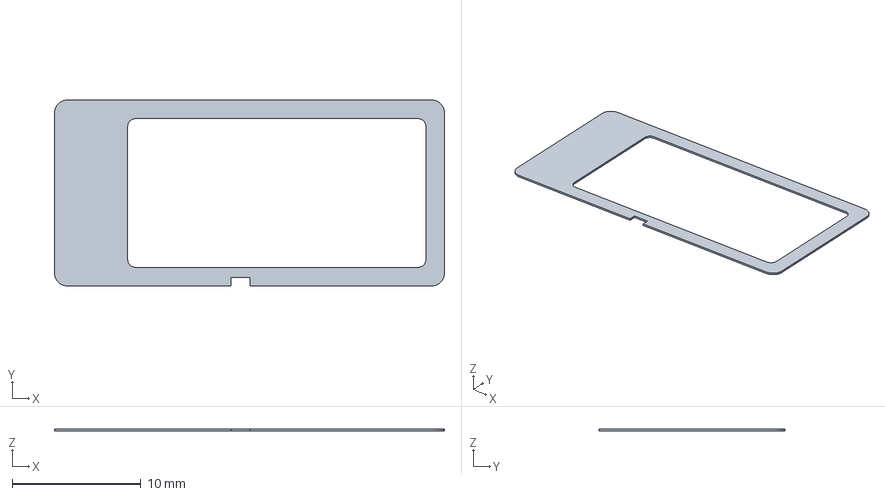
[picture p73: CAD file, 2026-10-07]
cad/out/variant-thin/tpu/bezel_gasket.3mf
30.3 x 14.4 x 0.16 mm
