backmeupplz/project-horae/hardware/rf/case/metal.stl

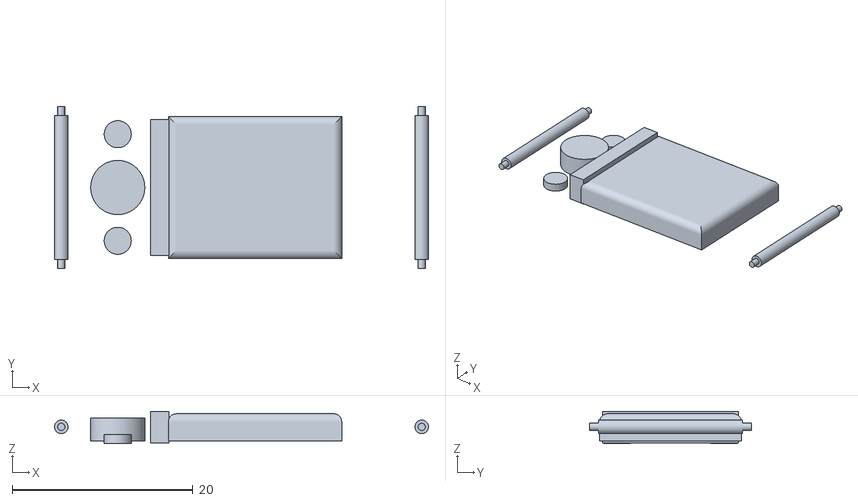
[picture p74: CAD file, 2026-10-07]
hardware/rf/case/metal.stl
41.4 x 17.9 x 3.55
