backmeupplz/project-horae/cad/out/plates/tpu.3mf

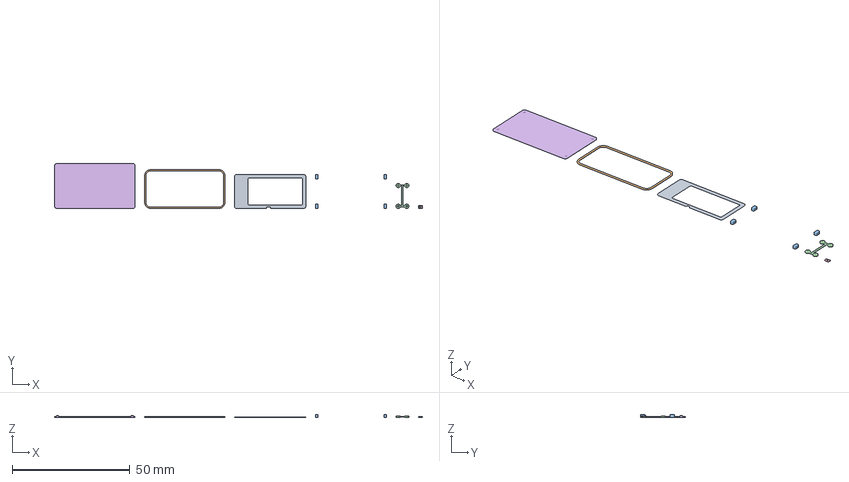
[picture p75: CAD file, 2026-10-07]
cad/out/plates/tpu.3mf
156.1 x 19.1 x 1.15 mm
bezel_gasket
bottom_seal
cushions
pogo_seals
mic_seal
dock_feet
