backmeupplz/project-horae/cad/out/variant-thin/tpu/pogo_seals.3mf

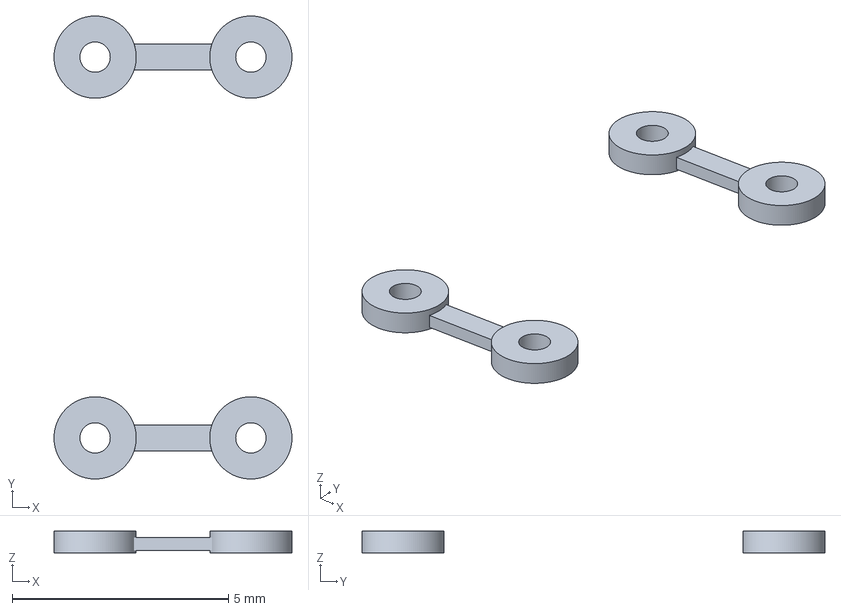
[picture p76: CAD file, 2026-10-07]
cad/out/variant-thin/tpu/pogo_seals.3mf
5.50 x 10.7 x 0.5 mm
