backmeupplz/project-horae/hardware/rf/case/tpu.stl

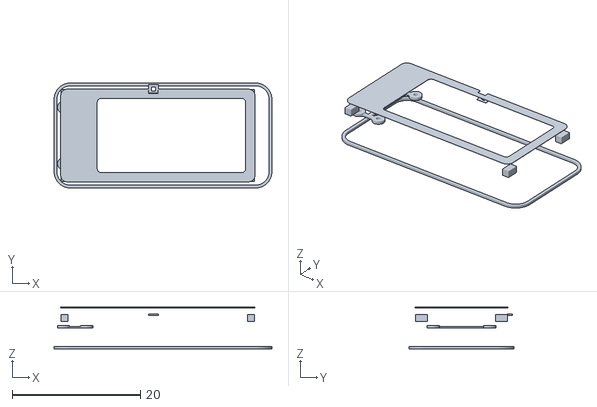
[picture p77: CAD file, 2026-10-07]
hardware/rf/case/tpu.stl
34.0 x 16.4 x 6.50
