backmeupplz/project-horae/hardware/rf/case/strap.stl

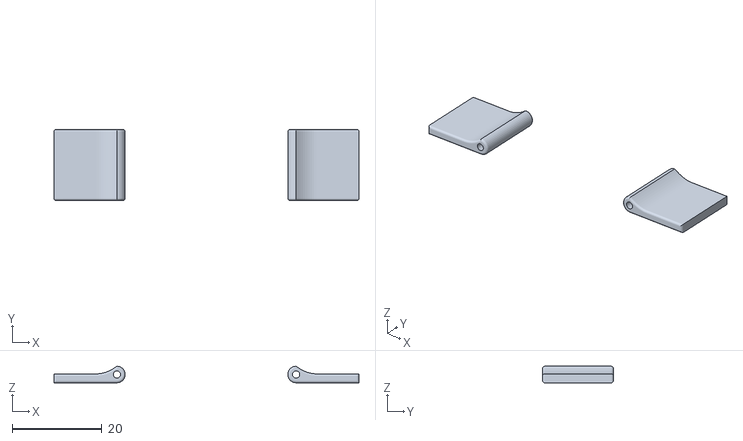
[picture p78: CAD file, 2026-10-06]
hardware/rf/case/strap.stl
67.9 x 15.8 x 3.70
