backmeupplz/project-horae/media/2026-10-05/cad-assembled.png

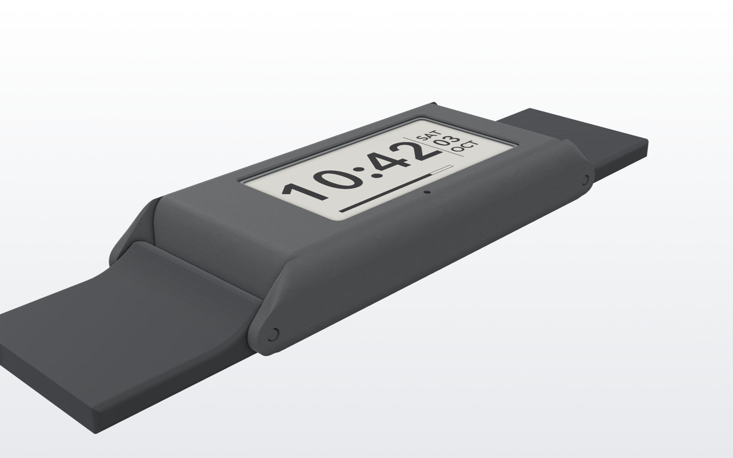
media/2026-10-05/cad-assembled.png
