backmeupplz/project-horae/media/2026-10-05/cad-assembly.png

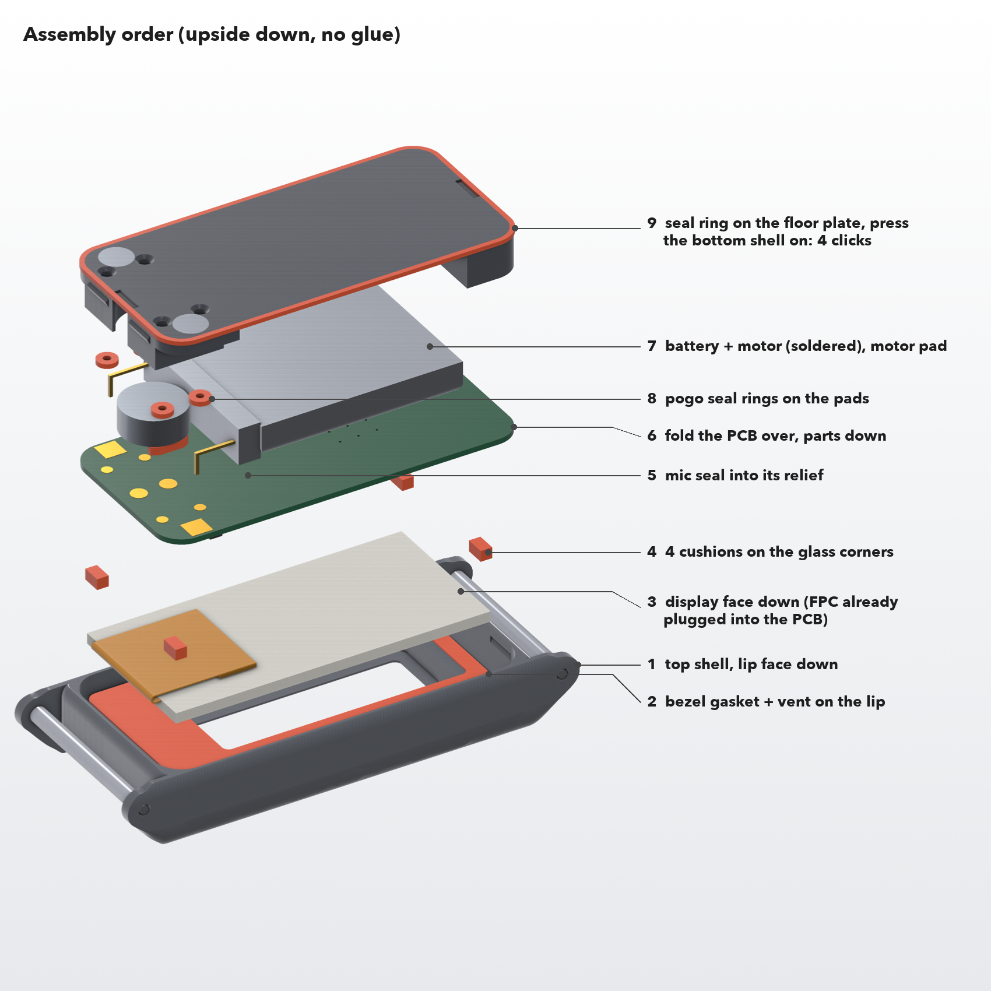
media/2026-10-05/cad-assembly.png
