backmeupplz/project-horae/media/2026-10-06/cad-dock-wiring.png

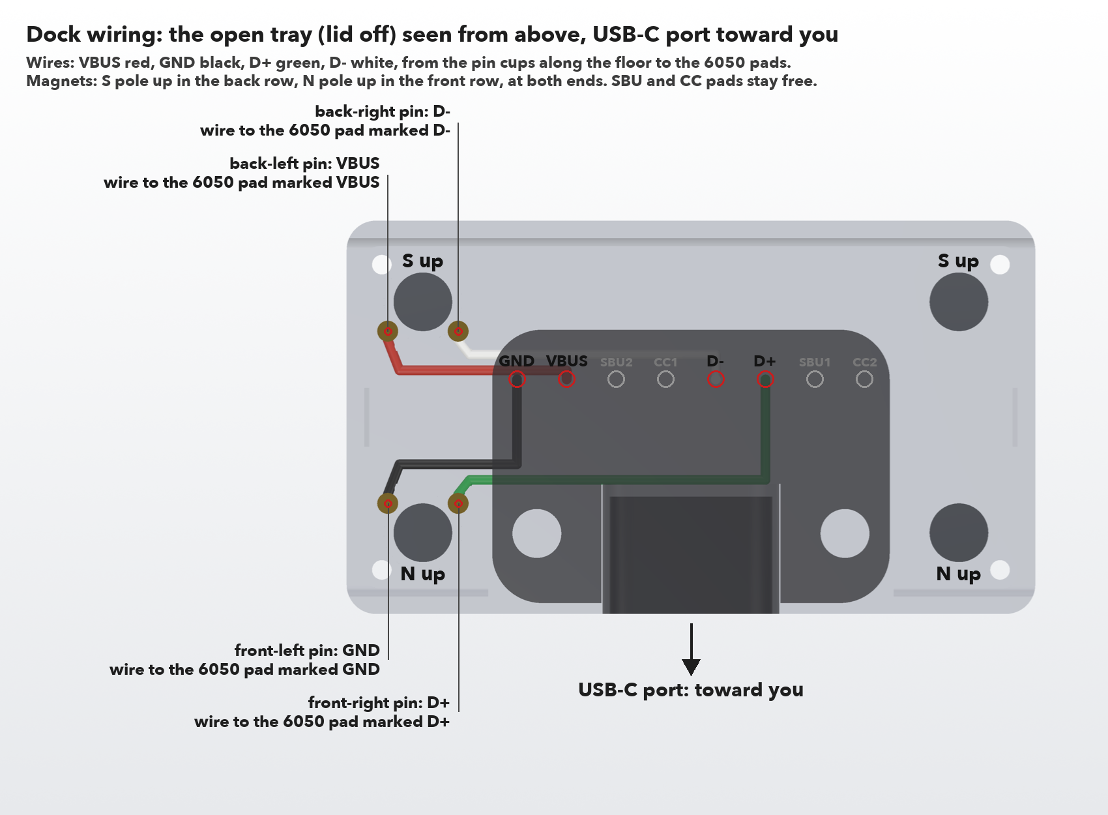
media/2026-10-06/cad-dock-wiring.png
